quadule/knobby/images/knobby2.jpg

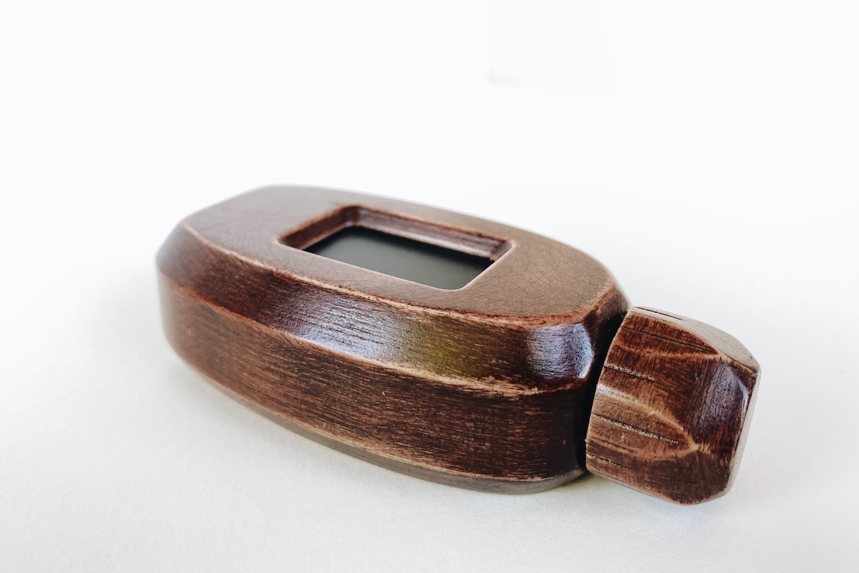
images/knobby2.jpg
