quadule/knobby/images/knobby5.jpg

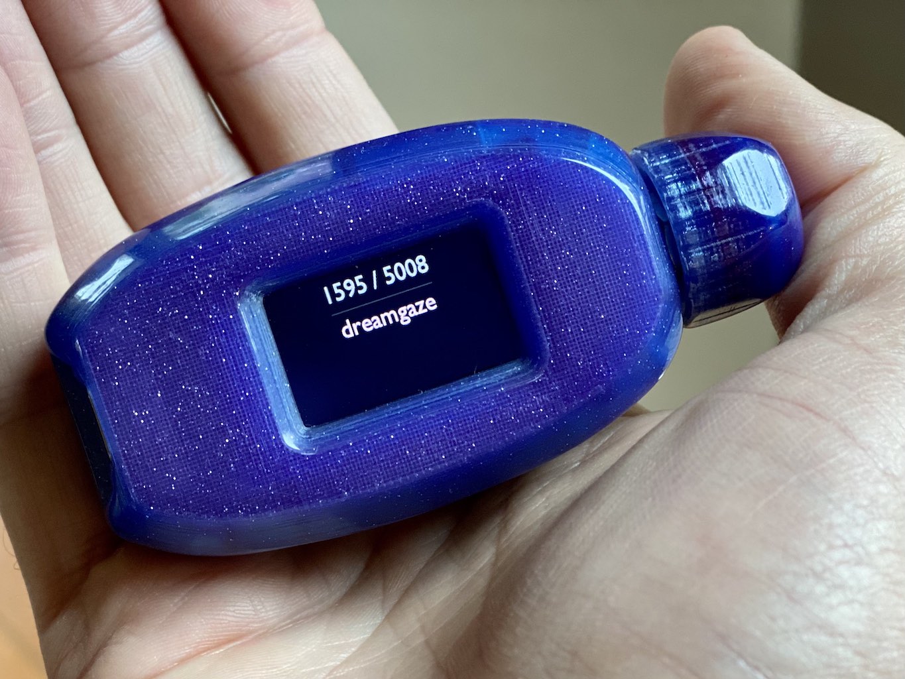
images/knobby5.jpg
