quadule/knobby/src/genres.h

#define GENRE_COUNT 6490
#define COUNTRY_COUNT 201

const char *genres[GENRE_COUNT] = { "2-step", "21st century classical", "432hz", "48g", "528hz", "5th gen k-pop", "5th wave emo", "8-bit", "8d", "a cappella", "a3", "aarhus indie", "aberdeen indie", "abstract", "abstract beats", "abstract hip hop", "abstract idm", "abstractro", "accordeon", "accordion", "accordion band", "acid house", "acid idm", "acid jazz", "acid rock", "acid techno", "acid trance", "acidcore", "acousmatic", "acoustic blues", "acoustic chill", "acoustic cover", "acoustic guitar cover", "acoustic opm", "acoustic pop", "acoustic punk", "acoustic rock", "action rock", "actors", "adelaide indie", "adelaide punk", "adivasi pop", "adoracao", "adoracion", "adoracion pentecostal", "adult standards", "adventista", "aesthetic rap", "afghan pop", "afghan rap", "afghan traditional", "african electronic", "african experimental", "african gospel", "african metal", "african percussion", "african reggae", "african rock", "african shoegaze", "african-american classical", "afrikaans", "afrikaans folk", "afrikaans gospel", "afrikaans gqom", "afrikaans hip hop", "afro drill", "afro house", "afro house angolano", "afro psych", "afro r&b", "afro soul", "afro-cuban percussion", "afro-cuban traditional", "afro-funk", "afrobeat", "afrobeat brasileiro", "afrobeat fusion", "afrobeats", "afrofuturism", "afrofuturismo brasileiro", "afropop", "afroswing", "aggressive phonk", "aggro chileno", "aggrotech", "aghani lil-atfal", "agronejo", "ai", "aikatsu", "ainu folk", "akordeon", "alabama hardcore", "alabama indie", "alabama metal", "alabama rap", "alandsk musik", "alaska hip hop", "alaska indie", "albanian alternative", "albanian folk", "albanian hip hop", "albanian iso polyphony", "albanian pop", "albanian rock", "albany ny indie", "alberta country", "alberta hip hop", "album rock", "albuquerque indie", "algerian folk", "algorave", "alpenpanorama", "alphorn", "alpine yodeling", "alt z", "alt-idol", "alte", "alternative americana", "alternative ccm", "alternative country", "alternative dance", "alternative emo", "alternative hardcore", "alternative hip hop", "alternative metal", "alternative metalcore", "alternative pop", "alternative pop rock", "alternative r&b", "alternative rock", "alternative roots rock", "amapiano", "ambeat", "ambient", "ambient black metal", "ambient country", "ambient dub", "ambient dub techno", "ambient folk", "ambient fusion", "ambient guitar", "ambient house", "ambient idm", "ambient industrial", "ambient lo-fi", "ambient pop", "ambient post-rock", "ambient psychill", "ambient synth", "ambient techno", "ambient trance", "ambient worship", "american 21st century classical", "american choir", "american classical piano", "american contemporary classical", "american early music", "american folk revival", "american grindcore", "american melodeath", "american metalcore", "american modern classical", "american oi", "american orchestra", "american post-punk", "american post-rock", "american primitive", "american romanticism", "american shoegaze", "amharic pop", "anadolu rock", "anarcho-punk", "ancient mediterranean", "andalusian classical", "andean flute", "andean panpipe", "anglican liturgy", "animal singing", "anime", "anime cv", "anime drill", "anime game", "anime hardstyle", "anime latino", "anime lo-fi", "anime phonk", "anime piano", "anime rap", "anime rock", "anime score", "animegrind", "ann arbor indie", "anthem", "anthem emo", "anthem worship", "anti-folk", "antideutsche", "antilliaanse folklore", "antilliaanse rap", "antiviral pop", "apostolic worship", "appalachian black metal", "appalachian folk", "appenzeller folk", "arab alternative", "arab electronic", "arab experimental", "arab folk", "arab groove", "arab metal", "arab pop", "arab trap", "arabesk", "arabic hip hop", "arabic instrumental", "arabic jazz", "argentine alternative rock", "argentine ambient", "argentine hardcore", "argentine heavy metal", "argentine hip hop", "argentine indie", "argentine indie rock", "argentine jazz", "argentine metal", "argentine punk", "argentine reggae", "argentine rock", "argentine telepop", "arizona punk", "arkansas country", "arkansas hip hop", "arkansas indie", "arkansas metal", "armenian folk", "armenian hip hop", "armenian indie", "armenian pop", "arpa grande", "arpa paraguaya", "arrocha", "arrochadeira", "ars subtilior", "art pop", "art punk", "art rock", "art song", "arunachal indie", "asakaa", "asbury park indie", "asheville indie", "asian american hip hop", "asmr", "assamese hip hop", "assamese pop", "assyrian pop", "athens indie", "atl drill", "atl hip hop", "atl trap", "atlanta bass", "atlanta indie", "atlanta metal", "atlanta punk", "atlantic canada hip hop", "atmosphere", "atmospheric black metal", "atmospheric dnb", "atmospheric doom", "atmospheric post-metal", "atmospheric post-rock", "atmospheric sludge", "auckland indie", "audiophile vocal", "aussie drill", "aussie emo", "aussietronica", "austin americana", "austin hip hop", "austin metal", "austin rock", "austin singer-songwriter", "austindie", "australian alt-country", "australian alternative pop", "australian alternative rock", "australian ambient", "australian americana", "australian black metal", "australian blues", "australian children's music", "australian choir", "australian classical", "australian classical piano", "australian comedy", "australian country", "australian dance", "australian death metal", "australian electropop", "australian experimental", "australian garage punk", "australian hardcore", "australian hip hop", "australian house", "australian indie", "australian indie folk", "australian indie rock", "australian indigenous hip hop", "australian indigenous music", "australian jazz", "australian metal", "australian metalcore", "australian pop", "australian post-hardcore", "australian post-punk", "australian post-rock", "australian psych", "australian r&b", "australian reggae fusion", "australian rock", "australian rockabilly", "australian shoegaze", "australian singer-songwriter", "australian ska", "australian surf rock", "australian talent show", "australian techno", "australian thrash metal", "australian trap", "australian underground hip hop", "austrian black metal", "austrian choir", "austrian classical piano", "austrian contemporary classical", "austrian dnb", "austrian hip hop", "austrian indie", "austrian jazz", "austrian metal", "austrian orchestra", "austrian pop", "austrian punk", "austrian stoner rock", "austrian techno", "austro-german modernism", "austropop", "auteur-compositeur-interprete quebecois", "autoharp", "autonomous black metal", "avant-garde", "avant-garde black metal", "avant-garde jazz", "avant-garde metal", "avant-prog", "avant-rock", "axe", "azeri alternative", "azeri pop", "azeri rap", "azeri traditional", "azonto", "azontobeats", "bachata", "bachata dominicana", "bachchon ke geet", "background jazz", "background jazz product", "background music", "background piano", "backing track", "baglama", "bagpipe", "bagpipe marching band", "baha'i", "bahamian folk", "bahamian pop", "baiao", "baithak gana", "baja indie", "bajan soca", "bajki", "bakersfield sound", "bal-musette", "balafon", "balalaika", "balearic", "balfolk", "bali indie", "balikpapan indie", "balinese traditional", "balkan beats", "balkan brass", "balkan classical piano", "balkan drill", "balkan folk metal", "balkan hip hop", "balkan post-punk", "balkan punk", "balkan trap", "ballet class", "ballroom", "balochi folk", "balochi pop", "baltic black metal", "baltic choir", "baltic classical", "baltic classical piano", "baltic folk", "baltic post-punk", "baltimore hip hop", "baltimore indie", "band organ", "banda", "banda carnavalera", "banda de bronces", "banda de viento", "banda guanajuatense", "banda jalisciense", "banda militar", "banda peruana", "banda sinaloense", "bandinhas", "bandolim", "bandoneon", "bandung indie", "bandura", "bangalore indie", "bangla gojol", "bangla pop", "bangladeshi hip hop", "bangladeshi indie", "bangladeshi rock", "banjara pop", "banjo", "bansuri", "baoule", "baps", "baptist gospel", "barbadian pop", "barbershop", "barcadi", "bard", "bardcore", "barnalog", "barnasogur", "barnemusikk", "barnmusik", "barnsagor", "barockinterpreten", "baroque", "baroque brass", "baroque cello", "baroque ensemble", "baroque pop", "baroque singing", "baroque violin", "baroque woodwind", "barrelhouse piano", "basel indie", "bases de freestyle", "basque folk", "bass house", "bass music", "bass trap", "bass trip", "basshall", "bassline", "batak", "bath indie", "batida", "batidao romantico", "baton rouge indie", "baton rouge rap", "batswana traditional", "battle rap", "bay area hip hop", "bay area indie", "bayerischer rap", "bboy", "bc underground hip hop", "beach house", "beach music", "beat italiano", "beat poetry", "beatboxing", "beatdown", "beatlesque", "beats", "bebop", "bedroom pop", "bedroom r&b", "bedroom skramz", "bedroom soul", "belarusian electronic", "belarusian hip hop", "belarusian indie", "belarusian metal", "belarusian pop", "belarusian punk", "belarusian rock", "belfast indie", "belfast metal", "belgian black metal", "belgian blues", "belgian classical piano", "belgian contemporary classical", "belgian dance", "belgian death metal", "belgian dnb", "belgian edm", "belgian electronic", "belgian experimental", "belgian hardcore", "belgian hip hop", "belgian indie", "belgian indie rock", "belgian jazz", "belgian metal", "belgian modern jazz", "belgian new wave", "belgian pop", "belgian post-rock", "belgian punk", "belgian rock", "belgian singer-songwriter", "belgian stoner rock", "belgian techno", "bells", "belly dance", "belo horizonte indie", "bemani", "benga", "bengali folk", "bengali metal", "beninese pop", "bergamo indie", "bergen indie", "berlin minimal techno", "berlin school", "bern indie", "bernu dziesmas", "bgm", "bhajan", "bhangra", "bhojpuri folk", "bhojpuri pop", "bhutanese pop", "bible", "big band", "big beat", "big room", "bikutsi", "binaural", "birdsong", "birmingham grime", "birmingham hip hop", "birmingham indie", "birmingham metal", "birthday", "bisaya indie", "bisaya rap", "bisaya worship", "bisrock", "bitpop", "black 'n' roll", "black americana", "black comedy", "black death", "black metal", "black metal argentino", "black noise", "black punk", "black sludge", "black speed metal", "black thrash", "blackened crust", "blackened deathcore", "blackened hardcore", "blackened screamo", "blackgaze", "blaskapelle", "blasmusik", "bleakgaze", "bleep techno", "bloco", "bluegrass", "bluegrass fiddle", "bluegrass gospel", "blues", "blues band", "blues latinoamericano", "blues mexicano", "blues rock", "blues-rock guitar", "bmore", "bodo pop", "boeremusiek", "bogor indie", "bohemian baroque", "bohol indie", "bolero", "bolero cubano", "bolero mexicano", "bolivian metal", "bolivian rock", "bolobedu house", "bomba", "bomba y plena", "bongo flava", "boogaloo", "boogie", "boogie-woogie", "boom bap", "boom bap brasileiro", "boom bap espanol", "bornehistorier", "borneo traditional", "bornesange", "bosnian electronic", "bosnian indie", "bosnian pop", "bossa nova", "bossa nova cover", "bossa nova jazz", "bossbeat", "bosstown sound", "boston drill", "boston electronic", "boston folk", "boston hardcore", "boston hip hop", "boston indie", "boston metal", "boston punk", "boston rock", "bothy ballad", "botswana hip hop", "botswana pop", "bounce", "bouncy house", "bouyon", "bouzouki", "bow pop", "boy band", "boy pop", "boy soprano", "bozlak", "brain waves", "braindance", "brasilia indie", "brass band", "brass band brasileiro", "brass band pop", "brass ensemble", "brass quintet", "brazilian bass", "brazilian black metal", "brazilian blues", "brazilian boogie", "brazilian ccm", "brazilian classical", "brazilian classical piano", "brazilian contemporary classical", "brazilian death metal", "brazilian dnb", "brazilian doom metal", "brazilian edm", "brazilian emo", "brazilian experimental", "brazilian gospel", "brazilian grindcore", "brazilian groove metal", "brazilian hardcore", "brazilian heavy metal", "brazilian hip hop", "brazilian house", "brazilian indie", "brazilian indie rock", "brazilian jazz", "brazilian lo-fi rock", "brazilian metal", "brazilian metalcore", "brazilian modern jazz", "brazilian percussion", "brazilian post-hardcore", "brazilian post-rock", "brazilian power metal", "brazilian progressive metal", "brazilian punk", "brazilian punk rock", "brazilian reggae", "brazilian rock", "brazilian rockabilly", "brazilian ska", "brazilian soul", "brazilian stoner rock", "brazilian straight edge", "brazilian surf rock", "brazilian tech house", "brazilian techno", "brazilian thrash metal", "breakbeat", "breakcore", "breaks", "brega", "brega funk", "brega paraense", "brega romantico", "brega saudade", "breton folk", "brighton indie", "brill building pop", "brisbane hip hop", "brisbane indie", "brisbane punk", "bristol electronic", "bristol indie", "brit funk", "britcore", "british alternative rock", "british black metal", "british blues", "british brass band", "british children's music", "british choir", "british classical piano", "british comedy", "british contemporary classical", "british country", "british dance band", "british death metal", "british electroacoustic", "british experimental", "british folk", "british grindcore", "british indie rock", "british industrial", "british invasion", "british jazz", "british math rock", "british modern classical", "british orchestra", "british post-rock", "british power metal", "british singer-songwriter", "british soul", "british soundtrack", "britpop", "britpop revival", "brno indie", "broadway", "brockton hip hop", "broken beat", "broken transmission", "bronx drill", "bronx hip hop", "brooklyn drill", "brooklyn indie", "brostep", "bruneian indie", "bruneian pop", "brutal death metal", "brutal deathcore", "brutal prog", "bubble trance", "bubblegrunge", "bubblegum bass", "bubblegum dance", "bubblegum pop", "buffalo hip hop", "buffalo ny indie", "buffalo ny metal", "bulgarian electronic", "bulgarian experimental", "bulgarian folk", "bulgarian hip hop", "bulgarian indie", "bulgarian metal", "bulgarian pop", "bulgarian r&b", "bulgarian rock", "bulgarian trap", "bullerengue", "burkinabe pop", "burkinabe traditional", "burmese pop", "burmese traditional", "burundian pop", "burundian traditional", "bury st edmunds indie", "bush ballad", "byzantine", "c-pop", "c-pop girl group", "c64", "c86", "cabaret", "cajun", "calgary indie", "cali rap", "california hardcore", "calming instrumental", "calypso", "cambodian pop", "cambodian rock", "cambodian traditional", "cambridge choir", "cambridgeshire indie", "cameroonian hip hop", "cameroonian pop", "campursari", "canadian americana", "canadian black metal", "canadian blues", "canadian ccm", "canadian celtic", "canadian children's music", "canadian choir", "canadian classical", "canadian classical piano", "canadian comedy", "canadian contemporary classical", "canadian contemporary country", "canadian contemporary r&b", "canadian country", "canadian death metal", "canadian drill", "canadian electronic", "canadian electropop", "canadian experimental", "canadian folk", "canadian garage rock", "canadian hardcore", "canadian hip hop", "canadian house", "canadian indie", "canadian indie folk", "canadian indie rock", "canadian indigenous hip hop", "canadian indigenous music", "canadian latin", "canadian metal", "canadian metalcore", "canadian modern jazz", "canadian old school hip hop", "canadian pop", "canadian pop punk", "canadian post-hardcore", "canadian post-punk", "canadian post-rock", "canadian psychedelic", "canadian psychedelic rock", "canadian punk", "canadian rock", "canadian rockabilly", "canadian shoegaze", "canadian singer-songwriter", "canadian soundtrack", "canadian stoner rock", "canadian trap", "canadian underground hip hop", "canberra indie", "cancion infantil latinoamericana", "cancion infantil mexicana", "cancion melodica", "cancoes infantis", "candombe", "candomble", "candy pop", "cantaditas", "cantautor", "cantautor catala", "cantautora argentina", "cantautora mexicana", "cante alentejano", "cante flamenco", "canterbury scene", "canti alpini", "canto a tenore", "canto popular uruguayo", "cantonese opera", "cantonese traditional", "cantonese worship", "cantopop", "canzone d'autore", "canzone genovese", "canzone napoletana", "canzone siciliane", "cape breton folk", "cape breton indie", "cape town indie", "cape verdean folk", "capoeira", "caracas indie", "cardiff indie", "caribbean metal", "carimbo", "carnatic", "carnatic instrumental", "carnatic vocal", "carnaval", "carnaval cadiz", "carnaval limburg", "cartoni animati", "cartoon", "cascadia psych", "cascadia shoegaze", "cascadian black metal", "catalan folk", "cathedral choir", "caucasian classical", "caucasian classical piano", "caucasian folk", "cavernous death metal", "ccm", "cdmx indie", "cdo indie", "cedm", "ceilidh", "cello", "cello ensemble", "celtic", "celtic harp", "celtic metal", "celtic punk", "celtic rock", "central american metal", "central asian folk", "central asian hip hop", "cerkes muzikleri", "ceske chvaly", "cha-cha-cha", "chaabi algerien", "chaabi marocain", "chabad niggunim", "chain punk", "chakma pop", "chakra", "chalga", "chamame", "chamame brasilero", "chamber choir", "chamber ensemble", "chamber folk", "chamber orchestra", "chamber pop", "chamber psych", "chamorro pop", "champeta", "channel islands indie", "channel pop", "chanson", "chanson humoristique", "chanson paillarde", "chanson quebecois", "chanson virale", "chant basque", "chant religieux", "chante nwel", "chaotic black metal", "chaotic hardcore", "chapel hill sound", "chapman stick", "charanga", "charango", "charlotte nc indie", "charlottesville indie", "charred death", "charva", "chasidic pop", "chattanooga indie", "chechen pop", "chennai indie", "chhattisgarhi pop", "chicago blues", "chicago bop", "chicago drill", "chicago hardcore", "chicago house", "chicago indie", "chicago mexican", "chicago pop punk", "chicago punk", "chicago rap", "chicago soul", "chicano punk", "chicano rap", "chicha", "chihuahua indie", "children's choir", "children's folk", "children's music", "children's story", "chilean black metal", "chilean hardcore", "chilean indie", "chilean metal", "chilean rock", "chilean techno", "chilena", "chill abstract hip hop", "chill baile", "chill beats", "chill breakcore", "chill dream pop", "chill drill", "chill groove", "chill guitar", "chill house", "chill lounge", "chill out", "chill phonk", "chill pop", "chill r&b", "chill-out trance", "chillhop", "chillstep", "chillsynth", "chillwave", "chimurenga", "chinderlieder", "chinese audiophile", "chinese bgm", "chinese black metal", "chinese classical", "chinese classical performance", "chinese classical piano", "chinese drama ost", "chinese electronic", "chinese electropop", "chinese experimental", "chinese folk", "chinese hip hop", "chinese hyperpop", "chinese idol pop", "chinese indie", "chinese indie pop", "chinese indie rock", "chinese instrumental", "chinese jazz", "chinese manyao", "chinese melodic rap", "chinese metal", "chinese metalcore", "chinese minyao", "chinese new year", "chinese opera", "chinese post-punk", "chinese post-rock", "chinese punk", "chinese r&b", "chinese reggae", "chinese singer-songwriter", "chinese soundtrack", "chinese talent show", "chinese traditional", "chinese viral pop", "chinese wind", "chinese worship", "chip hop", "chiptune", "chopped and screwed", "choral", "choro", "choro contemporaneo", "christchurch indie", "christelijk", "christian a cappella", "christian afrobeat", "christian alternative rock", "christian dance", "christian death metal", "christian deathcore", "christian doom metal", "christian hard rock", "christian hardcore", "christian hip hop", "christian indie", "christian indie folk", "christian lo-fi", "christian metal", "christian metalcore", "christian music", "christian pop", "christian power metal", "christian punk", "christian rock", "christian symphonic metal", "christian thrash metal", "christian trap", "christian uplift", "christlicher rap", "christmas", "christmas instrumental", "christmas product", "chutney", "cifteli", "cimbalom", "cimbalova muzika", "cincinnati indie", "cincinnati rap", "cinematic dubstep", "cinematic post-rock", "circassian folk", "circuit", "circus", "city pop", "clap and tap", "clarinet ensemble", "classic afrobeat", "classic anime", "classic arab pop", "classic assamese pop", "classic australian country", "classic azeri pop", "classic bangla pop", "classic belgian pop", "classic bhangra", "classic bollywood", "classic bulgarian pop", "classic canadian rock", "classic cantopop", "classic city pop", "classic colombian pop", "classic country pop", "classic czech pop", "classic danish pop", "classic danish rock", "classic disco polo", "classic dubstep", "classic dutch pop", "classic eurovision", "classic female blues", "classic finnish pop", "classic finnish rock", "classic french pop", "classic garage rock", "classic girl group", "classic greek pop", "classic greek rock", "classic hardstyle", "classic house", "classic hungarian pop", "classic hungarian rock", "classic icelandic pop", "classic indo pop", "classic indonesian rock", "classic iskelma", "classic israeli pop", "classic italian folk pop", "classic italian pop", "classic j-pop", "classic j-rock", "classic japanese jazz", "classic k-pop", "classic kollywood", "classic konkani pop", "classic korean pop", "classic latvian pop", "classic luk thung", "classic malaysian pop", "classic mandopop", "classic moroccan pop", "classic nepali pop", "classic norwegian pop", "classic nz country", "classic nz pop", "classic oklahoma country", "classic opm", "classic pakistani pop", "classic persian pop", "classic peruvian pop", "classic polish pop", "classic portuguese pop", "classic praise", "classic progressive house", "classic psychedelic rock", "classic punjabi pop", "classic rock", "classic romanian pop", "classic russian pop", "classic russian rock", "classic schlager", "classic sierreno", "classic sinhala pop", "classic soul", "classic soundtrack", "classic sudanese pop", "classic swedish pop", "classic texas country", "classic thai pop", "classic tollywood", "classic tunisian pop", "classic turkish pop", "classic uk pop", "classic ukrainian pop", "classic venezuelan pop", "classical", "classical accordion", "classical baritone", "classical bass", "classical bassoon", "classical cello", "classical clarinet", "classical contralto", "classical countertenor", "classical drill", "classical era", "classical flute", "classical guitar", "classical guitar duo", "classical guitar quartet", "classical harp", "classical horn", "classical jazz fusion", "classical mandolin", "classical mezzo-soprano", "classical oboe", "classical organ", "classical percussion", "classical performance", "classical piano", "classical piano duo", "classical piano quartet", "classical piano trio", "classical saxophone", "classical saxophone quartet", "classical soprano", "classical string trio", "classical tenor", "classical trombone", "classical trumpet", "classical tuba", "classify", "clawhammer banjo", "clean comedy", "cleveland indie", "cleveland metal", "cloud rap", "cloud rap francais", "coco", "cocuk masallari", "cocuk sarkilari", "coldwave", "collage pop", "college a cappella", "college marching band", "cologne electronic", "cologne hip hop", "cologne indie", "colombian black metal", "colombian death metal", "colombian electronic", "colombian hardcore", "colombian hip hop", "colombian indie", "colombian pop", "colombian rock", "color noise", "colorado hardcore", "columbus ohio indie", "combos nacionales", "comedia", "comedie musicale", "comedienne", "comedy", "comedy rap", "comedy rock", "comfy synth", "comic", "comic metal", "commons", "complextro", "compositional ambient", "comptine", "comptine africaine", "concepcion indie", "concert band", "concertina", "concurso de talentos argentino", "congolese gospel", "connecticut hardcore", "connecticut indie", "conscious hip hop", "contemporary choir", "contemporary classical", "contemporary classical piano", "contemporary country", "contemporary folk", "contemporary gospel", "contemporary jazz", "contemporary post-bop", "contemporary r&b", "contemporary vocal jazz", "contra dance", "contrabass", "convent", "cook islands pop", "cool jazz", "copla", "coptic hymn", "coral gospel", "corecore", "cork indie", "cornetas y tambores", "cornish folk", "cornwall indie", "corrido", "corridos adictivos", "corridos alternativos", "corridos belicos", "corridos clasicos", "corridos cristianos", "corridos tumbados", "corrosion", "corsican folk", "cosmic american", "cosmic black metal", "cosmic death metal", "cosmic post-rock", "cosmic uplifting trance", "country", "country blues", "country boogie", "country dawn", "country gospel", "country pop", "country quebecois", "country rap", "country road", "country rock", "countrygaze", "coupe-decale", "coventry indie", "cover acustico", "coverchill", "covertrance", "covertronica", "cowboy western", "cowpunk", "crack rock steady", "crank wave", "cristiana para ninos", "croatian electronic", "croatian folk", "croatian hip hop", "croatian indie", "croatian metal", "croatian pop", "croatian rock", "crossover prog", "crossover thrash", "cruise", "crunk", "crust punk", "cryptic black metal", "cuarteto", "cuatro puertorriqueno", "cuatro venezolano", "cuban alternative", "cuban electronic", "cuban funk", "cuban rumba", "cubaton", "cueca chilena", "cuento infantile", "cumbia", "cumbia 420", "cumbia amazonica", "cumbia andina mexicana", "cumbia boliviana", "cumbia chilena", "cumbia colombiana regia", "cumbia cristiana", "cumbia del sureste", "cumbia ecuatoriana", "cumbia editada", "cumbia funk", "cumbia lagunera", "cumbia paraguaya", "cumbia peruana", "cumbia pop", "cumbia ranchera", "cumbia salvadorena", "cumbia santafesina", "cumbia sonidera", "cumbia sonorense", "cumbia surena", "cumbia uruguaya", "cumbia villera", "cyber metal", "cybergrind", "cyberpunk", "cymraeg", "cypriot hip hop", "cypriot metal", "cypriot pop", "czech alternative rap", "czech classical", "czech classical piano", "czech contemporary classical", "czech country", "czech drill", "czech electronic", "czech experimental", "czech folk", "czech folk rock", "czech hardcore", "czech hip hop", "czech indie", "czech jazz", "czech metal", "czech pop", "czech pop rock", "czech psychedelic", "czech punk", "czech rock", "czech singer-songwriter", "czech swing", "czsk black metal", "czsk electropop", "czsk emo rap", "czsk hip hop", "czsk hyperpop", "czsk reggae", "czsk viral pop", "d-beat", "dabke", "dainuojamoji poezija", "dakke dak", "dalarna indie", "dallas indie", "dambora", "dance pop", "dance rock", "dance-punk", "dancefloor dnb", "dancehall", "dancehall chileno", "dancehall colombiano", "dancehall guyanaise", "dancehall mauricien", "dancehall queen", "dangdut", "dangdut koplo", "dangdut remix", "danish alternative rock", "danish black metal", "danish choir", "danish classical", "danish contemporary classical", "danish death metal", "danish electro", "danish electronic", "danish electropop", "danish experimental", "danish folk", "danish hardcore", "danish hip hop", "danish indie", "danish indie pop", "danish jazz", "danish metal", "danish modern jazz", "danish pop", "danish pop rock", "danish post-punk", "danish punk", "danish rock", "danish singer-songwriter", "danish techno", "dansband", "danseband", "dansei seiyu", "dansk comedy", "dansk lovsang", "dansktop", "danspunk", "danzon", "darbuka", "dariacore", "dark ambient", "dark black metal", "dark cabaret", "dark clubbing", "dark disco", "dark electro", "dark electro-industrial", "dark folk", "dark hardcore", "dark jazz", "dark minimal techno", "dark plugg", "dark pop", "dark post-punk", "dark progressive house", "dark psytrance", "dark r&b", "dark rock", "dark synthpop", "dark techno", "dark trap", "dark wave", "darkstep", "darksynth", "dayton indie", "dc hardcore", "dc indie", "death 'n' roll", "death doom", "death industrial", "death metal", "deathcore", "deathgrass", "deathgrind", "deathrash", "deathrock", "deathstep", "deboxe", "dechovka", "decije pesme", "deconstructed club", "deep acoustic pop", "deep active rock", "deep adult standards", "deep ambient", "deep big room", "deep brazilian pop", "deep breakcore", "deep ccm", "deep chill", "deep chill-out", "deep christian rock", "deep classic garage rock", "deep comedy", "deep contemporary country", "deep dance pop", "deep darkpsy", "deep deep house", "deep deep tech house", "deep delta blues", "deep disco", "deep disco house", "deep discofox", "deep dnb", "deep downtempo fusion", "deep dubstep", "deep east coast hip hop", "deep euro house", "deep eurodance", "deep filthstep", "deep flow", "deep folk metal", "deep free jazz", "deep freestyle", "deep full on", "deep funk", "deep funk house", "deep funk ostentacao", "deep g funk", "deep german hip hop", "deep german indie", "deep german punk", "deep gothic post-punk", "deep groove house", "deep happy hardcore", "deep hardcore", "deep hardcore punk", "deep hardtechno", "deep house", "deep idm", "deep indie pop", "deep indie rock", "deep indie singer-songwriter", "deep italo disco", "deep jazz fusion", "deep latin alternative", "deep latin christian", "deep latin jazz", "deep liquid", "deep liquid bass", "deep melodic death metal", "deep melodic hard rock", "deep melodic metalcore", "deep metalcore", "deep minimal techno", "deep motown", "deep neo-synthpop", "deep neofolk", "deep new americana", "deep new wave", "deep norteno", "deep northern soul", "deep orgcore", "deep pop edm", "deep pop emo", "deep power-pop punk", "deep progressive house", "deep progressive rock", "deep progressive trance", "deep psychobilly", "deep psytrance", "deep punk rock", "deep r&b", "deep ragga", "deep rai", "deep smooth jazz", "deep smooth r&b", "deep soft rock", "deep soul house", "deep soundtrack", "deep southern soul", "deep southern trap", "deep space rock", "deep sunset lounge", "deep surf music", "deep swedish rock", "deep symphonic black metal", "deep talent show", "deep tech house", "deep techno", "deep tropical house", "deep turkish pop", "deep underground hip hop", "deep uplifting trance", "deep vocal house", "deep vocal jazz", "delaware indie", "delta blues", "dembow", "dembow dominicano", "demoscene", "dennery segment", "denpa-kei", "denton tx indie", "denver indie", "denver metal", "denver rap", "depressive black metal", "derby indie", "derry indie", "desert blues", "desi emo rap", "desi hip hop", "desi pop", "desi trap", "dessin anime", "destroy techno", "detroit hardcore", "detroit hip hop", "detroit house", "detroit indie", "detroit rock", "detroit techno", "detroit trap", "detroit trap brasileiro", "detroit trap en espanol", "detske pesnicky", "detske pisnicky", "detski pesnichki", "detskie pesni", "detskie rasskazy", "deutsch disney", "deutschrock", "devon indie", "dfw rap", "dhrupad", "dicsoites", "didgeridoo", "digital hardcore", "dikir barat", "dinner jazz", "dirty south rap", "dirty texas rap", "disco", "disco house", "disco polo", "discofox", "disney", "disney dansk", "disney espanol", "disney horspiele", "disney italiano", "disney norsk", "disney piano", "disney polska", "disney portugues", "disney portugues brasil", "disney russian", "disney suomi", "disney svenska", "dissonant death metal", "diva house", "dixieland", "diy emo", "diy pop punk", "dizi", "djecje pjesme", "djembe", "djent", "dmv rap", "dogri pop", "dombra", "dominican indie", "dominican pop", "dong-yo", "doo-wop", "doom metal", "doomcore", "doomgaze", "dortmund indie", "double drumming", "doujin", "downtempo", "downtempo bass", "downtempo deathcore", "downtempo fusion", "draaiorgel", "draga", "dragspel", "drain", "drama", "dream plugg", "dream pop", "dream trance", "dreamgaze", "dreamo", "dreampunk", "dresden indie", "drift", "drift phonk", "drikkelek", "drill", "drill and bass", "drill beats", "drill brasileiro", "drill chileno", "drill dominicano", "drill espanol", "drill francais", "drill italiana", "drill tuga", "drone", "drone ambient", "drone folk", "drone metal", "drone psych", "drone rock", "dronescape", "drum and bass", "drumfunk", "drumless hip hop", "dub", "dub brasileiro", "dub metal", "dub poetry", "dub product", "dub punk", "dub reggae", "dub techno", "dublin indie", "dubstep", "dubstep product", "dubsteppe", "duduk", "duhovne pjesme", "duluth indie", "dundee indie", "dunedin indie", "dunedin sound", "dungeon rap", "dungeon synth", "duranguense", "dusseldorf electronic", "dusseldorf indie", "dutch americana", "dutch baroque", "dutch black metal", "dutch blues", "dutch cabaret", "dutch classical piano", "dutch contemporary classical", "dutch death metal", "dutch disney", "dutch dnb", "dutch drill", "dutch edm", "dutch experimental", "dutch experimental electronic", "dutch folk", "dutch hip hop", "dutch house", "dutch idol pop", "dutch indie", "dutch indie rock", "dutch jazz", "dutch metal", "dutch moombahton", "dutch musical", "dutch pop", "dutch post-punk", "dutch prog", "dutch punk", "dutch punk rock", "dutch r&b", "dutch rap pop", "dutch rock", "dutch shoegaze", "dutch singer-songwriter", "dutch stoner rock", "dutch tech house", "dutch trance", "dutch trap", "dutch underground hip hop", "dweilorkest", "dytyachi pisni", "early american folk", "early avant garde", "early french punk", "early modern classical", "early music", "early music choir", "early music ensemble", "early reggae", "early romantic era", "early synthpop", "early us punk", "east anglia indie", "east coast hip hop", "east coast reggae", "eastern bloc groove", "easy listening", "easycore", "eau claire indie", "ebm", "ecm-style jazz", "ectofolk", "ecuadorian alternative rock", "ecuadorian indie", "ecuadorian pop", "edinburgh indie", "edinburgh metal", "edm", "edmonton indie", "edo old school", "egg punk", "egyptian alternative", "egyptian hip hop", "egyptian metal", "egyptian pop", "egyptian rock", "egyptian traditional", "egyptian trap", "egyptian viral pop", "el paso indie", "electra", "electric bass", "electric blues", "electro", "electro bailando", "electro dub", "electro house", "electro jazz", "electro latino", "electro swing", "electro trash", "electro-industrial", "electro-pop francais", "electroacoustic composition", "electroacoustic improvisation", "electroclash", "electrofox", "electronic djent", "electronic rock", "electronic trap", "electronica", "electronica argentina", "electronica chilena", "electronica cristiana", "electronica peruana", "electronica venezuela", "electronicore", "electropop", "electropowerpop", "elektropunk", "elephant 6", "eletronica underground brasileira", "emo", "emo mexicano", "emo peruano", "emo punk", "emo rap", "emo rap italiano", "emo trap en espanol", "emo trap italiana", "emocore", "emoplugg", "emotional black metal", "emoviolence", "english baroque", "english indie rock", "english renaissance", "enka", "ensemble stars", "entehno", "environmental", "epa dunk", "epic black metal", "epic collage", "epic doom", "epicore", "epunk", "er ge", "erhu", "eritrean pop", "erotic product", "erotica", "erotik", "escape room", "esperanto", "essex indie", "estonian electronic", "estonian folk", "estonian hip hop", "estonian indie", "estonian jazz", "estonian metal", "estonian pop", "estonian rock", "ethereal gothic", "ethereal wave", "etherpop", "ethio-jazz", "ethiopian hip hop", "ethiopian pop", "ethiopian traditional", "ethnomusicology", "ethnotronica", "eugene indie", "euphonium", "euphoric hardstyle", "euro hi-nrg", "eurobeat", "eurodance", "europop", "euroska", "eurovision", "euskal indie", "euskal metal", "euskal musica", "euskal reggae", "euskal rock", "eventyr", "everything", "exotica", "experimental", "experimental ambient", "experimental bass", "experimental big band", "experimental black metal", "experimental classical", "experimental club", "experimental dub", "experimental dubstep", "experimental electronic", "experimental folk", "experimental guitar", "experimental hip hop", "experimental house", "experimental indie", "experimental indie rock", "experimental jazz", "experimental percussion", "experimental poetry", "experimental pop", "experimental psych", "experimental r&b", "experimental rock", "experimental synth", "experimental techno", "experimental vocal", "extratone", "fado", "fado antigo", "fado de coimbra", "fado instrumental", "fake", "fallen angel", "family gospel", "fan chant", "fantasy", "fantasy metal", "fantasy synth", "faroese folk", "faroese indie", "faroese jazz", "faroese pop", "faroese rock", "fast melodic punk", "festigal", "fictitious orchestra", "fidget house", "field recording", "field recording ambient", "fife and drum", "fijian pop", "filmi", "filter house", "filthstep", "final fantasy", "fingerstyle", "finlandssvenska musik", "finnish alternative rock", "finnish black metal", "finnish blues", "finnish choir", "finnish classical", "finnish contemporary classical", "finnish dance pop", "finnish death metal", "finnish doom metal", "finnish drill", "finnish edm", "finnish electro", "finnish electronic", "finnish experimental", "finnish folk", "finnish hard rock", "finnish hardcore", "finnish heavy metal", "finnish hip hop", "finnish idol pop", "finnish indie", "finnish jazz", "finnish melodeath", "finnish metal", "finnish metalcore", "finnish modern jazz", "finnish new wave", "finnish pop", "finnish pop punk", "finnish post-punk", "finnish power metal", "finnish progressive metal", "finnish progressive rock", "finnish psychedelic rock", "finnish punk", "finnish reggae", "finnish rockabilly", "finnish soul", "finnish tango", "finnish techno", "finnish trap", "finnish worship", "firenze indie", "fisarmonica", "flamenco", "flamenco electronica", "flamenco fusion", "flamenco guitar", "flamenco urbano", "flashcore", "flemish folk", "flick hop", "flint hip hop", "float house", "florida death metal", "florida drill", "florida hardcore", "florida rap", "flute rock", "fluxwork", "fnaf", "fnf", "fo jing", "focus", "focus beats", "focus trance", "fogo pentecostal", "folclor afrocolombiano", "folclor colombiano", "folclore castilla y leon", "folclore extremeno", "folclore jujeno", "folclore navarra", "folclore portugues", "folclore salteno", "folclore santiagueno", "folclore tucumano", "folk", "folk black metal", "folk brasileiro", "folk cantabria", "folk metal", "folk metal latinoamericano", "folk punk", "folk rock", "folk rock italiano", "folk siciliana", "folk-pop", "folklore argentino", "folklore boliviano", "folklore chileno", "folklore cuyano", "folklore ecuatoriano", "folklore nuevo argentino", "folklore panameno", "folklore paraguayo", "folklore peruano", "folklore quebecois", "folklore surero", "folklore uruguayo", "folklore venezolano", "folklore veracruzano", "folkmusik", "folktronica", "football", "footwork", "forest black metal", "forest psy", "forest synth", "forro", "forro de favela", "forro gospel", "forro instrumental", "forro manauara", "forro tradicional", "fort wayne indie", "fort worth indie", "fotbollslatar", "fourth world", "frafra", "franco-flemish school", "frankfurt electronic", "frankfurt indie", "frauenrap", "freak folk", "freakbeat", "free folk", "free improvisation", "free jazz", "freeform hardcore", "freestyle", "fremantle indie", "french baroque", "french black metal", "french classical piano", "french contemporary classical", "french death metal", "french dnb", "french dub", "french emo", "french experimental rock", "french folk", "french folk pop", "french garage rock", "french hardcore", "french hip hop", "french indie folk", "french indie pop", "french indietronica", "french jazz", "french metal", "french movie tunes", "french oi", "french opera", "french orchestra", "french pop", "french post-punk", "french post-rock", "french psychedelic", "french punk", "french reggae", "french renaissance", "french rock", "french rock-and-roll", "french rockabilly", "french romanticism", "french shoegaze", "french soundtrack", "french stoner rock", "french synthpop", "french tech house", "french techno", "french worship", "frenchcore", "frevo", "friese muziek", "fuji", "full on", "full on groove", "funana", "funeral doom", "funk", "funk 150 bpm", "funk bh", "funk capixaba", "funk carioca", "funk consciente", "funk das antigas", "funk evangelico", "funk mandelao", "funk melody", "funk metal", "funk mexicano", "funk mtg", "funk ostentacao", "funk paulista", "funk pop", "funk rj", "funk rock", "funk viral", "funktronica", "funky breaks", "funky house", "funky tech house", "furry", "fussball", "future ambient", "future bass", "future bounce", "future funk", "future garage", "future house", "future rock", "futurepop", "futuristic swag", "fvnky rimex", "g funk", "g-house", "gabber", "gabonese pop", "gaddiyali pop", "gaian doom", "gainesville indie", "gaita", "gaita colombiana", "gaita zuliana", "galante era", "galego", "galician folk", "galician indie", "galician jazz", "galician rock", "galway indie", "gambian hip hop", "gambian pop", "game mood", "gamecore", "gamelan", "gaming dubstep", "gaming edm", "gangster rap", "garage house", "garage pop", "garage psych", "garage punk", "garage punk blues", "garage rock", "garage rock mexicano", "garage rock revival", "garhwali pop", "garifuna folk", "garo pop", "gauze pop", "gay chorus", "gayageum", "gbvfi", "geek folk", "geek rock", "geinin song", "gen z singer-songwriter", "gengetone", "genshin", "georgian alternative", "georgian electronic", "georgian folk", "georgian hip hop", "georgian polyphony", "georgian pop", "georgian rock", "german alternative rap", "german alternative rock", "german baroque", "german black metal", "german blues", "german boom bap", "german ccm", "german choir", "german classical piano", "german cloud rap", "german contemporary classical", "german country", "german dance", "german dark minimal techno", "german death metal", "german dnb", "german drill", "german ebm", "german electronica", "german grindcore", "german hard rock", "german hardcore", "german heavy metal", "german hip hop", "german house", "german hyperpop", "german indie", "german indie folk", "german indie pop", "german indie rock", "german jazz", "german jazz rap", "german literature", "german melodeath", "german metal", "german metalcore", "german oi", "german opera", "german orchestra", "german pagan metal", "german pop", "german pop rock", "german post-hardcore", "german post-punk", "german post-rock", "german power metal", "german prog", "german punk", "german punk rock", "german r&b", "german reggae", "german renaissance", "german rock", "german rockabilly", "german romanticism", "german shoegaze", "german show tunes", "german singer-songwriter", "german ska", "german soundtrack", "german stoner rock", "german street punk", "german tech house", "german techno", "german thrash metal", "german trance", "german trap", "german underground rap", "german viral rap", "german worship", "ghanaian alternative", "ghanaian gospel", "ghanaian hip hop", "ghanaian pop", "ghanaian traditional", "ghazal", "ghent indie", "ghettotech", "ghibli", "ghoststep", "girl group", "glam metal", "glam punk", "glam rock", "glasgow indie", "glass", "glee club", "glitch", "glitch ambient", "glitch beats", "glitch hop", "glitch pop", "glitchbreak", "glitchcore", "glitter trance", "gnawa", "go-go", "goa hip hop", "goa psytrance", "goa trance", "gochiusa", "gogeo", "golden age hip hop", "gong", "goralski", "goregrind", "gorge", "gospel", "gospel amapiano", "gospel antigas", "gospel blues", "gospel drill", "gospel italiano", "gospel papiamento", "gospel r&b", "gospel rap", "gospel reggae", "gospel singers", "gospel soul", "gothabilly", "gothenburg hip hop", "gothenburg indie", "gothenburg metal", "gothic alternative", "gothic americana", "gothic black metal", "gothic doom", "gothic metal", "gothic post-punk", "gothic rock", "gothic symphonic metal", "gotico brasileiro", "gotlandsk musik", "gqom", "granada indie", "grand rapids indie", "grave wave", "graz indie", "grebo", "greek black metal", "greek clarinet", "greek contemporary classical", "greek downtempo", "greek drill", "greek fem rap", "greek folk", "greek guitar", "greek hip hop", "greek house", "greek indie", "greek indie rock", "greek jazz", "greek metal", "greek pop", "greek post-punk", "greek psychedelic rock", "greek punk", "greek rock", "greek shoegaze", "greek swing", "greek techno", "greek trap", "greek underground rap", "greenlandic pop", "gregorian chant", "gregorian dance", "grenada soca", "grim death metal", "grime", "grime brasileiro", "grimewave", "grindcore", "griot", "grisly death metal", "groove gospel", "groove metal", "groove room", "grunge", "grunge argentina", "grunge brasileiro", "grunge pop", "grunge revival", "grungegaze", "grunneger muziek", "grupera", "gruperas inmortales", "grupero romantico", "guadalajara indie", "guam indie", "guaracha", "guaracha santiaguena", "guatemalan indie", "guatemalan metal", "guatemalan pop", "guggenmusik", "guidance", "guided meditation", "guinean pop", "guitar case", "guitarra andina", "guitarra argentina", "guitarra clasica", "guitarra mexicana", "guitarra portuguesa", "gujarati garba", "gujarati pop", "gulf hip hop", "gumbe", "gundam", "guqin", "guyanese pop", "guzheng", "gwoka", "gyerekdalok", "gym hardstyle", "gym phonk", "gymcore", "gypsy", "gypsy fusion", "gypsy jazz", "gypsy punk", "h8000", "haitian dance", "haitian gospel", "haitian traditional", "haitian vodou drumming", "hakkapop", "halftime dnb", "halifax indie", "halloween", "hamburg electronic", "hamburg hip hop", "hamburg indie", "hamburger schule", "hamilton on indie", "hammered dulcimer", "hammond organ", "hampton roads indie", "handbells", "handpan", "hands up", "hangoskonyvek", "happy hardcore", "hard alternative", "hard bass", "hard bop", "hard chime", "hard dance", "hard glam", "hard house", "hard industrial techno", "hard minimal techno", "hard motivation", "hard rock", "hard rock brasileiro", "hard rock mexicano", "hard stoner rock", "hard techno", "hard trance", "hardcore", "hardcore breaks", "hardcore hip hop", "hardcore punk", "hardcore punk espanol", "hardcore techno", "hardgroove", "hardingfele", "hardstyle", "hardtekk", "hardvapour", "hardwave", "hare krishna", "harlem hip hop", "harlem renaissance", "harmonica blues", "harmonica jazz", "harmonikka", "harp", "harpsichord", "harsh noise wall", "haryanvi hip hop", "haryanvi pop", "haryanvi ragni", "hauntology", "haur kantak", "hausa pop", "hawaiian", "hawaiian hip hop", "hawaiian indie", "hawaiian punk", "hazaragi pop", "healing", "healing hz", "heartland rock", "heavy alternative", "heavy gothic rock", "heavy psych", "hel", "heligonka", "hengelliset laulut", "hexd", "hi-nrg", "hi-tech", "high vibe", "high-tech minimal", "highlife", "himachali pop", "himalayan folk", "himene tarava", "hindi hip hop", "hindi indie", "hindi worship", "hindustani classical", "hindustani instrumental", "hindustani vocal", "hinos ccb", "hip hop", "hip hop boliviano", "hip hop cubano", "hip hop galsen", "hip hop mauritanien", "hip hop quebecois", "hip hop reunionnais", "hip hop timur", "hip hop tuga", "hip house", "hip pop", "hip-hop experimental", "hipco", "hiplife", "histoire pour enfants", "historic classical performance", "historic orchestral performance", "historic piano performance", "historic string quartet", "historical keyboard", "historically informed performance", "hjemmesnekk", "hk-pop", "hmong pop", "ho munda", "hoerspiel", "hokkaido indie", "hokkien pop", "hollywood", "hololive", "honeyworks", "hong kong hip hop", "hong kong indie", "hong kong rock", "hong kong tv drama", "honky tonk", "honky-tonk piano", "hopebeat", "horn ensemble", "horo", "horror punk", "horror punk brasileiro", "horror synth", "horrorcore", "hot jazz", "house", "house argentino", "houston indie", "houston rap", "huapango", "huayno", "huayno peruano", "huayno popular", "hula", "hull indie", "humour francais", "humppa", "hungarian black metal", "hungarian choir", "hungarian classical performance", "hungarian classical piano", "hungarian contemporary classical", "hungarian edm", "hungarian folk", "hungarian hip hop", "hungarian indie", "hungarian metal", "hungarian pop", "hungarian punk", "hungarian rock", "hungarian techno", "hungarian underground rap", "huqin", "hurdy-gurdy", "huzunlu sarkilar", "hyper-rock", "hyperpop", "hyperpop brasileiro", "hyperpop en espanol", "hyperpop francais", "hyperpop italiano", "hypertechno", "hypertrance", "hyphy", "hypnagogic pop", "hypnosis", "hypnosis mic", "hypnotic techno", "icelandic black metal", "icelandic choir", "icelandic classical", "icelandic electronic", "icelandic experimental", "icelandic folk", "icelandic hip hop", "icelandic indie", "icelandic jazz", "icelandic metal", "icelandic pop", "icelandic post-punk", "icelandic punk", "icelandic rock", "icelandic singer-songwriter", "icelandic traditional", "idaho hip hop", "idaho indie", "idol", "idol game", "idol kayo", "idol rock", "igbo pop", "igbo rap", "igbo traditional", "igbo trap", "igbo worship", "ilahije", "ilahiler", "illbient", "ilocano pop", "impressionism", "indian ambient", "indian classical", "indian edm", "indian electronic", "indian folk", "indian fusion", "indian indie", "indian instrumental", "indian instrumental rock", "indian jazz", "indian lo-fi", "indian metal", "indian percussion", "indian rock", "indian singer-songwriter", "indian techno", "indian underground rap", "indian violin", "indiana hip hop", "indiana indie", "indie anthem-folk", "indie arequipeno", "indie asturiana", "indie boliviano", "indie campechano", "indie canario", "indie cantabria", "indie caribe colombiano", "indie catala", "indie catracho", "indie cordoba", "indie cristao", "indie curitibano", "indie dream pop", "indie electronica", "indie electropop", "indie emo", "indie emo rock", "indie extremena", "indie folk", "indie folk argentino", "indie folk italiano", "indie fuzzpop", "indie game soundtrack", "indie garage rock", "indie hidalguense", "indie hidrocalido", "indie hip hop", "indie huancaino", "indie jazz", "indie liguria", "indie michoacano", "indie napoletano", "indie nica", "indie nordeste argentino", "indie paraense", "indie platense", "indie poblano", "indie pop", "indie pop rap", "indie pop rock", "indie poptimism", "indie psych-pop", "indie psychedelic rock", "indie punk", "indie quebecois", "indie queretano", "indie r&b", "indie rock", "indie rock colombiano", "indie rock italiano", "indie rock mexicano", "indie rock peruano", "indie rockism", "indie salvadoreno", "indie shoegaze", "indie siciliano", "indie singer-songwriter", "indie soul", "indie sudcaliforniano", "indie surf", "indie tabasqueno", "indie tico", "indie triste", "indie trujillano", "indie tucumano", "indie valenciana", "indie veneto", "indie viet", "indiecoustica", "indietronica", "indonesian alternative rock", "indonesian bamboo", "indonesian black metal", "indonesian blues", "indonesian city pop", "indonesian death metal", "indonesian deathcore", "indonesian edm", "indonesian electronic", "indonesian emo", "indonesian emo rap", "indonesian experimental", "indonesian folk", "indonesian folk pop", "indonesian gothic metal", "indonesian hardcore", "indonesian hip hop", "indonesian hyperpop", "indonesian idol pop", "indonesian indie", "indonesian indie pop", "indonesian indie rock", "indonesian indigenous traditional", "indonesian jazz", "indonesian lo-fi pop", "indonesian metal", "indonesian neo-psychedelia", "indonesian pop", "indonesian pop punk", "indonesian pop rock", "indonesian post-hardcore", "indonesian post-punk", "indonesian psychedelia", "indonesian punk", "indonesian r&b", "indonesian reggae", "indonesian rock", "indonesian shoegaze", "indonesian singer-songwriter", "indonesian ska", "indonesian stoner rock", "indonesian thrash metal", "indonesian trap", "indonesian underground hip hop", "indonesian viral pop", "indonesian worship", "indorock", "industrial", "industrial black metal", "industrial hardcore", "industrial hip hop", "industrial metal", "industrial noise", "industrial pop", "industrial rock", "industrial techno", "indy indie", "inland empire hardcore", "instrumental acoustic guitar", "instrumental black metal", "instrumental bluegrass", "instrumental death metal", "instrumental djent", "instrumental funk", "instrumental grime", "instrumental hip hop", "instrumental lullaby", "instrumental math rock", "instrumental post-rock", "instrumental progressive metal", "instrumental rock", "instrumental soul", "instrumental stoner rock", "instrumental surf", "instrumental worship", "intelligent dance music", "inuit pop", "inuit traditional", "iowa hip hop", "iowa indie", "iranian experimental", "iranian metal", "iraqi hip hop", "irish accordion", "irish ballad", "irish banjo", "irish black metal", "irish classical", "irish contemporary classical", "irish country", "irish dance", "irish death metal", "irish drill", "irish electronic", "irish experimental", "irish experimental electronic", "irish fiddle", "irish flute", "irish folk", "irish gaelic folk", "irish hardcore", "irish hip hop", "irish indie", "irish indie rock", "irish metal", "irish modern jazz", "irish neo-traditional", "irish pop", "irish post-punk", "irish pub song", "irish punk", "irish rebel song", "irish rock", "irish shoegaze", "irish singer-songwriter", "irish techno", "irish trap", "irish underground rap", "iskelma", "islamic recitation", "isle of man indie", "isle of wight indie", "israeli classical", "israeli classical piano", "israeli folk", "israeli hip hop", "israeli indie", "israeli jazz", "israeli mediterranean", "israeli metal", "israeli pop", "israeli punk", "israeli rock", "israeli singer-songwriter", "israeli techno", "israeli traditional", "israeli trap", "israelite hip hop", "italian adult pop", "italian alternative", "italian baritone", "italian baroque", "italian baroque ensemble", "italian bass", "italian black metal", "italian blues", "italian choir", "italian classical guitar", "italian classical piano", "italian contemporary classical", "italian contemporary jazz", "italian death metal", "italian doom metal", "italian electronica", "italian emo", "italian experimental", "italian folk", "italian folk metal", "italian gothic", "italian gothic metal", "italian hardcore", "italian heavy metal", "italian hip hop", "italian indie pop", "italian industrial", "italian jazz", "italian jazz fusion", "italian library music", "italian lounge", "italian mandolin", "italian metal", "italian metalcore", "italian mezzo-soprano", "italian modern prog", "italian new wave", "italian occult psychedelia", "italian opera", "italian orchestra", "italian pop", "italian pop punk", "italian pop rock", "italian post-hardcore", "italian post-punk", "italian post-rock", "italian power metal", "italian progressive metal", "italian progressive rock", "italian punk", "italian reggae", "italian renaissance", "italian rockabilly", "italian romanticism", "italian screamo", "italian ska", "italian soprano", "italian soundtrack", "italian stoner rock", "italian tech house", "italian techno", "italian tenor", "italian trance", "italian underground hip hop", "italian violin", "italo beats", "italo dance", "italo disco", "italo house", "italogaze", "izvorna muzika", "j-acoustic", "j-ambient", "j-core", "j-division", "j-idol", "j-indie", "j-metal", "j-pixie", "j-pop", "j-pop boy group", "j-pop girl group", "j-poprock", "j-punk", "j-rap", "j-reggae", "j-rock", "jackin' house", "jacksonville indie", "jain bhajan", "jalsat", "jam band", "jamaican dancehall", "jamaican hip hop", "jamaican ska", "jamgrass", "jamtronica", "jangle pop", "jangle rock", "japanese alternative pop", "japanese alternative rock", "japanese beats", "japanese bedroom pop", "japanese black metal", "japanese blues", "japanese boom bap", "japanese buddhist chant", "japanese celtic", "japanese chill rap", "japanese chillhop", "japanese choir", "japanese classical", "japanese classical performance", "japanese classical piano", "japanese concert band", "japanese contemporary classical", "japanese dance pop", "japanese death metal", "japanese disney", "japanese dream pop", "japanese drill", "japanese dub", "japanese edm", "japanese electronic", "japanese electropop", "japanese emo", "japanese experimental", "japanese flute", "japanese folk", "japanese garage rock", "japanese girl punk", "japanese guitar", "japanese hardcore", "japanese heavy metal", "japanese house", "japanese hyperpop", "japanese idm", "japanese indie folk", "japanese indie pop", "japanese indie rock", "japanese instrumental", "japanese jazz", "japanese jazz fusion", "japanese jazztronica", "japanese juke", "japanese math rock", "japanese melodic hardcore", "japanese melodic punk", "japanese metalcore", "japanese new wave", "japanese old school hip hop", "japanese orchestra", "japanese piano", "japanese pop punk", "japanese pop rap", "japanese post-hardcore", "japanese post-punk", "japanese post-rock", "japanese power metal", "japanese prog", "japanese progressive house", "japanese psychedelic", "japanese psychedelic rock", "japanese punk rock", "japanese r&b", "japanese rockabilly", "japanese screamo", "japanese shoegaze", "japanese singer-songwriter", "japanese ska", "japanese soul", "japanese soundtrack", "japanese techno", "japanese teen pop", "japanese traditional", "japanese trap", "japanese underground rap", "japanese vgm", "japanese viral pop", "japanese vocal jazz", "japanese vtuber", "japanese worship", "japanoise", "javanese dangdut", "javanese gamelan", "jaw harp", "jawaiian", "jazz", "jazz accordion", "jazz blues", "jazz boliviano", "jazz boom bap", "jazz brass", "jazz caraibes", "jazz catala", "jazz chileno", "jazz clarinet", "jazz colombiano", "jazz composition", "jazz cover", "jazz cubano", "jazz dominicano", "jazz double bass", "jazz drums", "jazz flute", "jazz funk", "jazz fusion", "jazz guitar", "jazz guitar trio", "jazz harp", "jazz house", "jazz metal", "jazz mexicano", "jazz orchestra", "jazz organ", "jazz piano", "jazz pop", "jazz puertorriqueno", "jazz quartet", "jazz rap", "jazz rock", "jazz saxophone", "jazz tico", "jazz trio", "jazz trombone", "jazz trumpet", "jazz tuba", "jazz venezolano", "jazz vibraphone", "jazz violin", "jazz worship", "jazzcore", "jazztronica", "jazzy dnb", "jersey club", "jesus movement", "jewish a capella", "jewish cantorial", "jewish hip hop", "jewish pop", "jig and reel", "jirai kei", "jordanian alternative", "jordanian pop", "joropo", "josei rap", "joseon pop", "jota aragonesa", "jovem guarda", "judaica", "jug band", "jugendchor", "juju", "jump blues", "jump up", "jumpstyle", "jumptek", "jungle", "junior eurovision", "junior songfestival", "k-indie", "k-pop", "k-pop ballad", "k-pop boy group", "k-pop girl group", "k-pop reality show", "k-rap", "k-rock", "kaba gaida", "kabarett", "kabyle", "kabyle moderne", "kadongo kamu", "kalmar indie", "kamba pop", "kamen rider", "kaneka", "kannada bhava geethe", "kannada hip hop", "kannada indie", "kannada pop", "kansai indie", "kansas city hip hop", "kansas hip hop", "kansas indie", "kantele", "kapa haka", "karadeniz pop", "karadeniz turkuleri", "karaoke", "karbi pop", "karelian folk", "karen pop", "karneval", "karntner volksmusik", "kaseko", "kashmiri hip hop", "kashmiri pop", "kasi rap", "kavkaz", "kawaii edm", "kawaii future bass", "kawaii metal", "kayokyoku", "kazakh hip hop", "kazakh indie", "kazakh pop", "kazakh traditional", "kazakh viral pop", "kc indie", "keller synth", "kelowna bc indie", "kent indie", "kentucky hip hop", "kentucky indie", "kentucky metal", "kentucky mountain folk", "kentucky punk", "kentucky roots", "kenyan alternative", "kenyan drill", "kenyan hip hop", "kenyan pop", "kenyan r&b", "kenyan traditional", "kerkkoor", "kermis", "keroncong", "khaleeji iraqi", "khaliji", "khandeshi pop", "khasi pop", "khayal", "khmer", "khmer hip hop", "khortha pop", "kids dance party", "kids hip hop", "kikuyu gospel", "kikuyu pop", "kinderchor", "kinderliedjies", "kindermusik", "kindie rock", "king of prism", "kingston on indie", "kinnauri pop", "kirtan", "kiwi rock", "kizomba", "kizomba antigas", "kizomba cabo-verdiana", "klapa", "kleine hoerspiel", "kleinkunst", "klezmer", "klubowe", "knoxville indie", "kodomo no ongaku", "kokborok pop", "kol isha", "koledy", "koligeet", "kolkata indie", "kollywood", "kolo", "kolsche karneval", "komedi", "kompa", "kompa chretien", "kompa gouyad", "konkani pop", "konsrock", "kora", "korean bl ost", "korean city pop", "korean classical performance", "korean classical piano", "korean contemporary classical", "korean dream pop", "korean drill", "korean electronic", "korean electropop", "korean experimental", "korean hardcore", "korean hyperpop", "korean indie folk", "korean indie rock", "korean instrumental", "korean jazz", "korean metal", "korean minyo", "korean musicals", "korean old school hip hop", "korean ost", "korean phantom singer", "korean pop", "korean punk", "korean r&b", "korean shoegaze", "korean singer-songwriter", "korean soundtrack", "korean superband", "korean talent show", "korean traditional", "korean trap", "korean underground rap", "korean worship", "kosovan folk", "kosovan indie", "kosovan pop", "koto", "krajiska muzika", "krautrock", "krishnacore", "kritika", "krushclub", "krushfunk", "kuduro", "kuduro antigo", "kumaoni pop", "kundalini", "kundiman", "kurdish folk", "kurdish hip hop", "kurdish pop", "kurdish remix", "kurdish rock", "kwaito", "kyrgyz hip hop", "kyrgyz pop", "kyrgyz traditional", "kyushu indie", "la hardcore", "la indie", "la pop", "laboratorio", "ladakhi pop", "lafayette indie", "lagu aceh", "lagu bali", "lagu betawi", "lagu bugis", "lagu iban", "lagu jambi", "lagu jawa", "lagu karo", "lagu lampung", "lagu madura", "lagu maluku", "lagu manado", "lagu melayu", "lagu sabahan", "lagu sasak", "lagu sunda", "lagu tarling", "lagu timur", "lai hla", "laiko", "lambadao", "lampung indie", "lancashire indie", "lancaster pa indie", "landler", "language", "lao hip hop", "lao pop", "lao traditional", "lapland hip hop", "lapland metal", "lastelaulud", "lasten satuja", "lata", "late romantic era", "latin", "latin afrobeat", "latin alternative", "latin american baroque", "latin american classical piano", "latin american heavy psych", "latin arena pop", "latin christian", "latin classical", "latin funk", "latin hip hop", "latin house", "latin jazz", "latin metal", "latin pop", "latin rock", "latin shoegaze", "latin ska", "latin soundtrack", "latin surf rock", "latin talent show", "latin tech house", "latin tek", "latin viral pop", "latin viral rap", "latin worship", "latincore", "latino comedy", "latintronica", "latinx alternative", "latmiya", "latvian electronic", "latvian folk", "latvian hip hop", "latvian indie", "latvian metal", "latvian pop", "latvian rock", "laulaja-lauluntekija", "lawrence ks indie", "lds", "lds instrumental", "lds youth", "lebanese indie", "lebanese pop", "leeds indie", "leicester indie", "leipzig electronic", "leipzig indie", "leon gto indie", "lesen", "lesotho traditional", "levenslied", "lexington ky indie", "lezginka", "lgbtq+ hip hop", "liberian pop", "library music", "libyan hip hop", "libyan pop", "liechtenstein", "liedermacher", "light music", "lilith", "limerick indie", "liminal space", "lincoln ne indie", "lion city hardcore", "liquid funk", "lithuanian edm", "lithuanian electronic", "lithuanian folk", "lithuanian hip hop", "lithuanian indie", "lithuanian jazz", "lithuanian metal", "lithuanian pop", "lithuanian rock", "lithuanian trap", "little rock indie", "liverpool indie", "livetronica", "lldm", "lo star", "lo-fi", "lo-fi beats", "lo-fi brasileiro", "lo-fi chill", "lo-fi cover", "lo-fi emo", "lo-fi house", "lo-fi indie", "lo-fi jazzhop", "lo-fi latino", "lo-fi product", "lo-fi rap", "lo-fi sleep", "lo-fi study", "lo-fi vgm", "lok dohori", "lombok indie", "london indie", "london on indie", "london rap", "long island punk", "louange", "louisiana blues", "louisiana metal", "louisville indie", "louisville underground", "lounge", "lounge house", "louvor", "louvor icm", "louvores pentecostais", "love live", "lovecraftian metal", "lovers rock", "lowercase", "lowlands hardcore", "luk thung", "lullaby", "lund indie", "lustrum", "lute", "luxembourgian electronic", "luxembourgian hip hop", "luxembourgian indie", "luxembourgian metal", "luxembourgian pop", "macau pop", "macedonian electronic", "macedonian folk", "macedonian hip hop", "macedonian indie", "macedonian metal", "macedonian pop", "macedonian rock", "macross", "madchester", "madrigal", "maga rap", "maghreb", "maghreb metal", "magyar alternative", "magyar kabare", "magyar mulatos", "magyar musicalek", "magyar retro dance", "magyar trap", "mahraganat", "maidcore", "maimouna", "maine hip hop", "maine indie", "mainland chinese pop", "mainland se asia metal", "maithili", "makina", "makossa", "malagasy folk", "malagasy pop", "malang indie", "malang punk", "malawian folk", "malawian gospel", "malawian hip hop", "malawian pop", "malay rap", "malayalam cover", "malayalam hip hop", "malayalam indie", "malayalam madh", "malayalam pop", "malayalam worship", "malaysian hardcore", "malaysian hip hop", "malaysian indie", "malaysian mandopop", "malaysian metal", "malaysian pop", "malaysian post-rock", "malaysian punk", "malaysian tamil pop", "malaysian tamil rap", "malaysian traditional", "maldivian pop", "malian blues", "malian traditional", "mallet", "mallsoft", "malmo indie", "maloya", "maltese hip hop", "maltese metal", "maltese pop", "maluku pop", "mambo", "mambo chileno", "man's orchestra", "manchester hip hop", "manchester indie", "mande pop", "mandible", "mandolin", "mandopop", "manele", "manguebeat", "manila sound", "manipuri pop", "manitoba country", "manitoba indie", "manso indie", "mantra", "mapouka", "mappila paattu", "maracatu", "marathi balgeet", "marathi devotional", "marathi hip hop", "marathi pop", "marathi remix", "marathi traditional", "marcha funebre", "marching band", "marci brijuzi", "mariachi", "mariachi cristiano", "marimba", "marimba de guatemala", "marimba mexicana", "marimba orquesta", "marinera", "marrabenta", "marsmuziek", "martial industrial", "marwadi pop", "mashcore", "mashup", "maskandi", "massage", "math pop", "math rock", "math rock latinoamericano", "mathcore", "mathgrind", "mazandarani folk", "mbalax", "mbira", "mecha", "medieval", "medieval black metal", "medieval ensemble", "medieval folk", "medieval rock", "medimeisterschaften", "meditation", "medway sound", "meenawati", "mega funk", "melancholia", "melanesian pop", "melbourne bounce", "melbourne bounce international", "melbourne hip hop", "melbourne indie", "melbourne punk", "mellow gold", "melodic black metal", "melodic death metal", "melodic deathcore", "melodic doom", "melodic drill", "melodic dubstep", "melodic groove metal", "melodic hard rock", "melodic hardcore", "melodic house", "melodic metal", "melodic metalcore", "melodic power metal", "melodic progressive metal", "melodic rap", "melodic techno", "melodic thrash", "melodipop", "meme", "meme rap", "memphis americana", "memphis blues", "memphis hip hop", "memphis indie", "memphis phonk", "memphis soul", "men chika", "men's choir", "mento", "merengue", "merengue tipico", "merida indie", "merseybeat", "messianic praise", "mestissatge", "metal", "metal baiano", "metal balear", "metal catala", "metal catarinense", "metal cearense", "metal colombiano", "metal cover", "metal cristao", "metal ecuatoriano", "metal galego", "metal gaucho", "metal gotico", "metal guitar", "metal mineiro", "metal noir quebecois", "metal nortista", "metal paraguayo", "metal paranaense", "metal pernambucano", "metal piauiense", "metal salvadoreno", "metal tico", "metal uruguayo", "metalcore", "metalcore espanol", "metallic hardcore", "metis fiddle", "metropopolis", "mevlevi sufi", "mewati pop", "mexican black metal", "mexican classic rock", "mexican classical", "mexican death metal", "mexican edm", "mexican electronic", "mexican experimental", "mexican hardcore", "mexican hip hop", "mexican indie", "mexican metal", "mexican pop", "mexican pop punk", "mexican post-rock", "mexican power metal", "mexican rock", "mexican rock-and-roll", "mexican son", "mexican tech house", "mexican techno", "mexican thrash metal", "mexican traditional", "meyxana", "mezmur", "mezwed", "mgpjr", "miami bass", "miami electronic", "miami hip hop", "miami indie", "miami metal", "michigan folk", "michigan indie", "microhouse", "microsound", "microtonal", "middle earth", "middle east hip hop", "middle eastern black metal", "middle eastern traditional", "midwest americana", "midwest emo", "midwest shoegaze", "milan indie", "military band", "military cadence", "military rap", "milwaukee hip hop", "milwaukee indie", "min'yo", "mincecore", "mindfulness", "minecraft", "minimal dnb", "minimal dub", "minimal dubstep", "minimal melodic techno", "minimal synth", "minimal tech house", "minimal techno", "minimal wave", "minimalism", "minneapolis indie", "minneapolis metal", "minneapolis punk", "minneapolis sound", "minnesang", "minnesota hip hop", "minnesota metal", "mising pop", "mississippi hip hop", "mississippi indie", "missouri indie", "mizo gospel", "mizo pop", "mizrahi", "mluvene slovo", "mod revival", "modern alternative pop", "modern alternative rock", "modern bhajan", "modern big band", "modern blues", "modern blues rock", "modern bollywood", "modern cello", "modern chamber music", "modern country pop", "modern country rock", "modern darkwave", "modern downshift", "modern dream pop", "modern ebm", "modern electroacoustic", "modern enka", "modern folk rock", "modern free jazz", "modern funk", "modern goth", "modern hard rock", "modern hardcore", "modern indie folk", "modern indie pop", "modern j-rock", "modern jangle pop", "modern jazz piano", "modern jazz trio", "modern jungle", "modern melodic hardcore", "modern mod", "modern old-time", "modern performance", "modern power pop", "modern progressive rock", "modern psychedelic folk", "modern reggae", "modern rock", "modern salsa", "modern ska punk", "modern southern rock", "modern string quartet", "modern swing", "modern uplift", "moderne ludovky", "modular synth", "modular techno", "molam", "moldovan pop", "mollywood", "mongolian alternative", "mongolian folk", "mongolian hip hop", "mongolian pop", "montana indie", "montana metal", "montana roots", "montenegrin pop", "monterrey indie", "montreal indie", "moog", "moombahton", "moorish traditional", "moravian folk", "morelos indie", "morna", "moroccan pop", "moroccan rock", "moroccan traditional", "motivation", "motown", "mountain dulcimer", "movie tunes", "mpb", "mpb gospel", "multidisciplinary", "mumbai indie", "mundart", "munich electronic", "munich indie", "murcia indie", "murga", "music box", "music hall", "musica acoriana", "musica acreana", "musica afroperuana", "musica aguascalentense", "musica alagoana", "musica amapaense", "musica andina", "musica andina chilena", "musica andina colombiana", "musica andorra", "musica angolana", "musica antigua", "musica aragonesa", "musica ayacuchana", "musica baiana", "musica bajacaliforniana", "musica bautista", "musica blumenauense", "musica brasiliense", "musica cabo-verdiana", "musica calabrese", "musica campechana", "musica campineira", "musica campista", "musica canaria", "musica capixaba", "musica caririense", "musica catalana", "musica catarinense", "musica cearense", "musica chiapaneca", "musica chihuahuense", "musica coahuilense", "musica colimense", "musica colombiana instrumental", "musica costarricense", "musica costena", "musica criolla", "musica crista reformada", "musica cristiana guatemalteca", "musica de fondo", "musica de intervencao", "musica duranguense", "musica ecuatoguineana", "musica eletronica brasileira", "musica eletronica gospel", "musica etnica", "musica evangelica instrumental", "musica feirense", "musica folk asturiana", "musica gaucha", "musica gaucha tradicionalista", "musica goiana", "musica guerrerense", "musica guineense", "musica hondurena", "musica indigena brasileira", "musica indigena latinoamericana", "musica indigena mexicana", "musica infantil", "musica infantil catala", "musica instrumental cristiana", "musica istmena", "musica jalisciense", "musica jibara", "musica juiz-forana", "musica llanera", "musica lombarda", "musica londrinense", "musica madeirense", "musica mallorquina", "musica mapuche", "musica maranhense", "musica maringaense", "musica mato-grossense", "musica menorquina", "musica mexicana", "musica mexiquense", "musica michoacana", "musica mixteca", "musica mocambicana", "musica mogiana", "musica morelense", "musica nayarita", "musica neoleonesa", "musica nicaraguense", "musica nortena chilena", "musica nublensina", "musica oaxaquena", "musica occitana", "musica otavalena", "musica para criancas", "musica para ninos", "musica paraibana", "musica paranaense", "musica per bambini", "musica pernambucana", "musica piauiense", "musica piemonteisa", "musica pitiusa", "musica poblana", "musica ponta-grossense", "musica popular amazonense", "musica popular colombiana", "musica popular mineira", "musica popular paraense", "musica popular uruguaya", "musica portuguesa contemporanea", "musica potiguar", "musica potosina", "musica prehispanica", "musica puntana", "musica purepecha", "musica queretana", "musica quintanarroense", "musica rapa nui", "musica rondoniense", "musica roraimense", "musica sammarinese", "musica santomense", "musica sarda", "musica sergipana", "musica sinaloense", "musica sinfonica", "musica sonorense", "musica sudcaliforniana", "musica sul-mato-grossense", "musica tabasquena", "musica tamaulipeca", "musica timor-leste", "musica tlaxcalteca", "musica tocantinense", "musica tradicional cubana", "musica tradicional dominicana", "musica triste brasileira", "musica tropical guatemalteca", "musica urbana oaxaquena", "musica valenciana", "musica wixarika", "musica yucateca", "musical advocacy", "musicas espiritas", "musiikkia lapista", "musiikkia lapsille", "musik anak-anak", "musikkorps", "musiqi-ye zanan", "musique acadienne", "musique alsacienne", "musique ancienne", "musique centrafricaine", "musique comorienne", "musique concrete", "musique guadeloupe", "musique mahoraise", "musique mandingue", "musique mariage algerien", "musique mauritanienne", "musique militaire", "musique nigerienne", "musique peule", "musique pour enfant quebecois", "musique pour enfants", "musique soninke", "musique tahitienne", "musique tchadienne", "musique touareg", "musique traditionnelle comorienne", "musique traditionnelle congolaise", "musique urbaine brazzaville", "musique urbaine kinshasa", "muzica ardeleneasca", "muzica banateana", "muzica bisericeasca", "muzica copii", "muzica crestina", "muzica etno", "muzica lautareasca", "muzica maramureseana", "muzica moldoveneasca", "muzica populara", "muzica usoara", "muziek voor kinderen", "muzika l'yeladim", "myanmar gospel", "myanmar hip hop", "myanmar indie", "naat", "nadaswaram", "nagaland indie", "nagpuri pop", "naija old school", "naija worship", "namibian pop", "nantes indie", "narco rap", "narodna muzika", "narodnozabavna", "nasheed", "nashville americana", "nashville hip hop", "nashville indie", "nashville singer-songwriter", "nashville sound", "nasyid", "native american black metal", "native american contemporary", "native american flute", "native american hip hop", "native american metal", "native american spiritual", "native american traditional", "naturjodel", "navajo", "ndombolo", "neapolitan funk", "necrogrind", "necrotrap", "nederlandse hardstyle", "nederpop", "nederreggae", "neo classical metal", "neo grime", "neo honky tonk", "neo kyma", "neo mellow", "neo metal", "neo r&b", "neo soul", "neo soul-jazz", "neo-classical", "neo-crust", "neo-industrial rock", "neo-kraut", "neo-manele", "neo-pagan", "neo-progressive", "neo-proto", "neo-psicodelia brasileira", "neo-psychedelic", "neo-rockabilly", "neo-shibuya-kei", "neo-singer-songwriter", "neo-synthpop", "neo-trad doom metal", "neo-trad metal", "neo-trad prog", "neo-traditional bluegrass", "neo-traditional country", "neoclassical darkwave", "neoclassicism", "neofolk", "neomelodici", "neon pop punk", "neoperreo", "neotango", "nepali indie", "nepali metal", "nepali pop", "nepali rock", "nephop", "nerdcore", "nerdcore brasileiro", "neru", "neue deutsche harte", "neue deutsche todeskunst", "neue deutsche welle", "neue neue deutsche welle", "neue volksmusik", "neurofunk", "neurostep", "new age", "new age piano", "new americana", "new beat", "new brunswick indie", "new comedy", "new delhi indie", "new england americana", "new england black metal", "new england emo", "new england experimental", "new england hardcore", "new england metal", "new england shoegaze", "new french touch", "new hampshire indie", "new isolationism", "new italo disco", "new jack smooth", "new jack swing", "new jersey hardcore", "new jersey indie", "new jersey punk", "new jersey rap", "new jersey underground rap", "new mexico music", "new orleans americana", "new orleans blues", "new orleans funk", "new orleans indie", "new orleans jazz", "new orleans rap", "new orleans soul", "new rave", "new romantic", "new school turkce rap", "new tejano", "new tribe", "new wave", "new wave of glam metal", "new wave of osdm", "new wave of screamo", "new wave of speed metal", "new wave of thrash metal", "new wave pop", "new weird america", "new weird finland", "new york death metal", "new york drill", "new york shoegaze", "new zealand classical", "newcastle indie", "newcastle nsw indie", "newfoundland indie", "ney", "ngoni", "nhac thieu nhi", "nice indie", "nigerian hip hop", "nigerian pop", "night drive phonk", "nightcore", "nightrun", "nijisanji", "ninja", "nintendocore", "nisiotika", "nitzhonot", "nl folk", "no beat", "no wave", "noel quebecois", "nohay", "noise", "noise pop", "noise punk", "noise rock", "noisecore", "nordic ambient", "nordic classical piano", "nordic contemporary classical", "nordic folk", "nordic folk metal", "nordic house", "nordic orchestra", "nordic post-rock", "nordic shoegaze", "nordic soundtrack", "nordnorsk musikk", "nordnorsk ponk", "nordnorsk rap", "normal indie", "norman ok indie", "norrbotten indie", "norrlandsk hip hop", "norsk lovsang", "norske viser", "norteno", "norteno-sax", "north alabama indie", "north carolina emo", "north carolina hip hop", "north carolina indie", "north carolina metal", "north carolina roots", "north dakota indie", "north east england indie", "north moroccan rap", "northamptonshire indie", "northeast indian hip hop", "northeast indian indie", "northern irish indie", "northern irish punk", "northern soul", "northumbrian folk", "northwest china indie", "norwegian alternative rock", "norwegian americana", "norwegian black metal", "norwegian blues", "norwegian choir", "norwegian classical", "norwegian contemporary jazz", "norwegian country", "norwegian death metal", "norwegian doom metal", "norwegian experimental", "norwegian folk", "norwegian folk rock", "norwegian gospel", "norwegian hardcore", "norwegian hip hop", "norwegian house", "norwegian indie", "norwegian jazz", "norwegian metal", "norwegian pop", "norwegian pop rap", "norwegian prog", "norwegian psychedelic", "norwegian punk", "norwegian punk rock", "norwegian rock", "norwegian singer-songwriter", "norwegian space disco", "norwegian techno", "norwegian trap", "nottingham hip hop", "nottingham indie", "nouvelle chanson francaise", "nova canco", "nova mpb", "nova musica amazonense", "nova musica carioca", "nova musica maranhense", "nova musica paulista", "nova musica pernambucana", "novelty", "novo rock gaucho", "novos talentos brasileiros", "nu age", "nu disco", "nu electro", "nu gabber", "nu gaze", "nu jazz", "nu metal", "nu skool breaks", "nu-cumbia", "nu-metalcore", "nubian traditional", "nueva cancion", "nueva ola chilena", "nueva ola peruana", "nueva trova chilena", "nuevo flamenco", "nuevo folklore argentino", "nuevo folklore mexicano", "nuevo tango", "nurnberg indie", "nursery", "nwobhm", "nwocr", "nwothm", "ny roots", "nyahbinghi", "nyc club", "nyc indie rock", "nyc metal", "nyc pop", "nyc rap", "nyckelharpa", "nyhc", "nz alternative rock", "nz children's music", "nz christian", "nz dnb", "nz electronic", "nz folk", "nz gangsta rap", "nz hardcore", "nz hip hop", "nz indie", "nz jazz", "nz metal", "nz pop", "nz post-punk", "nz punk", "nz reggae", "nz singer-songwriter", "oakland hip hop", "oakland indie", "oaxaca indie", "oberkrainer", "oc indie", "oc rap", "occult black metal", "ocean", "oceania soundtrack", "odia bhajan", "odia pop", "oeteldonk", "ogene", "ohangla", "ohio hardcore", "ohio hip hop", "ohio indie", "oi", "ok indie", "okc indie", "okinawan folk", "okinawan pop", "oklahoma country", "oktoberfest", "old school atlanta hip hop", "old school bassline", "old school dancehall", "old school ebm", "old school hard trance", "old school highlife", "old school hip hop", "old school nederhop", "old school rap francais", "old school thrash", "old school uk hip hop", "old west", "old-time", "old-time fiddle", "oldschool deutschrap", "olympia wa indie", "omaha indie", "one-person band", "ontario indie", "opera", "opera chorus", "opera metal", "operatic pop", "operetta", "opm", "oratory", "orchestra", "orchestral performance", "orchestral soundtrack", "orebro indie", "organetto", "organic ambient", "organic electronic", "organic house", "orgcore", "oriental classical", "oriental metal", "orkiestra symfoniczna", "orkney and shetland folk", "orlando indie", "oromo pop", "orquesta cubana", "orquesta tipica", "orquesta tropical", "orquestas de galicia", "orthodox chant", "oshare kei", "oslo indie", "ostrock", "ostschlager", "otacore", "oth indie", "otroske pesmice", "ottawa indie", "ottawa rap", "oud", "oulu indie", "oulu metal", "outer hip hop", "outlaw country", "outsider", "outsider house", "oxford choir", "oxford indie", "oyun havasi", "p funk", "p-pop", "pacific islands gospel", "pacific islands pop", "pagan black metal", "pagode", "pagode baiano", "pagode novo", "pahadi pop", "paidika tragoudia", "paisley underground", "pakistani electronic", "pakistani folk", "pakistani hip hop", "pakistani indie", "pakistani pop", "pakistani rock", "palestinian alternative", "palestinian hip hop", "palestinian pop", "palestinian traditional", "palm desert scene", "palm wine guitar", "panamanian indie", "panamanian pop", "panamanian rock", "panpipe", "pansori", "papuan traditional", "papuri", "paracana", "paraguayan indie", "paraguayan rock", "parody", "partido alto", "partyschlager", "pashto pop", "pasodobles", "pastoral", "pei indie", "pennsylvania hardcore", "pennsylvania shoegaze", "permanent wave", "perreo", "persian alternative", "persian drill", "persian electronic", "persian hip hop", "persian melodic rap", "persian neo-traditional", "persian poetry", "persian pop", "persian rock", "persian sad rap", "persian traditional", "persian trap", "persian underground hip hop", "perth hip hop", "perth indie", "peruvian death metal", "peruvian experimental", "peruvian hip hop", "peruvian indie", "peruvian metal", "peruvian punk", "peruvian rock", "pet calming", "philly drill", "philly indie", "philly rap", "philly soul", "phleng phuea chiwit", "phoenix indie", "phonk", "phonk brasileiro", "piada", "pianissimo", "piano blues", "piano cover", "piano house", "piano mpb", "piano rock", "piano worship", "pibroch", "picopop", "piedmont blues", "pilates", "pink noise", "pinoy alternative rap", "pinoy alternative rock", "pinoy city pop", "pinoy drill", "pinoy edm", "pinoy hip hop", "pinoy idol pop", "pinoy indie", "pinoy indie rock", "pinoy metal", "pinoy pop punk", "pinoy praise", "pinoy r&b", "pinoy reggae", "pinoy rock", "pinoy shoegaze", "pinoy singer-songwriter", "pinoy traditional", "pinoy trap", "pipa", "pirate", "piratenmuziek", "piseiro", "pittsburgh indie", "pittsburgh indie rock", "pittsburgh metal", "pittsburgh rap", "pittsburgh rock", "pixel", "pixie", "plena uruguaya", "plug brasileiro", "plugg", "plugg en espanol", "plugg francais", "pluggnb", "plunderphonics", "png pop", "poetry", "poezja spiewana", "pohadky", "pokemon", "polca paraguaya", "police band", "polish alternative", "polish alternative rap", "polish alternative rock", "polish ambient", "polish black metal", "polish blues", "polish choir", "polish classical", "polish classical piano", "polish contemporary classical", "polish death metal", "polish drill", "polish early music", "polish electronica", "polish emo", "polish experimental", "polish experimental electronic", "polish folk", "polish folk metal", "polish free jazz", "polish hardcore", "polish hip hop", "polish indie", "polish indie rock", "polish jazz", "polish metal", "polish metalcore", "polish modern jazz", "polish noise rock", "polish old school hip hop", "polish phonk", "polish pop", "polish post-punk", "polish post-rock", "polish prog", "polish psychedelia", "polish punk", "polish reggae", "polish rock", "polish shoegaze", "polish synthpop", "polish techno", "polish thrash metal", "polish trap", "polish underground rap", "polish viral pop", "polish viral rap", "political hip hop", "polka", "polka nortena", "polynesian hip hop", "polynesian traditional", "polyphonies corses", "polyphony", "pontian folk", "pontianak indie", "pony", "pop", "pop ambient", "pop argentino", "pop boliviano", "pop catracho", "pop chileno", "pop costarricense", "pop cristiano", "pop dance", "pop edm", "pop electronico", "pop emo", "pop flamenco", "pop folk", "pop house", "pop lgbtq+ brasileira", "pop minang", "pop nacional", "pop nacional antigas", "pop paraguayo", "pop peruano", "pop punk", "pop quebecois", "pop r&b", "pop rap", "pop rap brasileiro", "pop reggaeton", "pop rock", "pop rock brasileiro", "pop romantico", "pop soul", "pop teen brasileiro", "pop urbaine", "pop venezolano", "pop violin", "pop virale italiano", "pop worship", "popgaze", "popping", "pops orchestra", "popullore jugu", "popwave", "pornogrind", "porro", "portland hip hop", "portland indie", "portland metal", "portland punk", "portsmouth indie", "portuguese black metal", "portuguese classical", "portuguese contemporary classical", "portuguese death metal", "portuguese early music", "portuguese electronic", "portuguese experimental", "portuguese folk", "portuguese hardcore", "portuguese indie", "portuguese indie rock", "portuguese jazz", "portuguese metal", "portuguese pop", "portuguese post-rock", "portuguese rock", "portuguese techno", "post-black metal", "post-disco", "post-disco soul", "post-doom metal", "post-grunge", "post-hardcore", "post-hardcore chileno", "post-metal", "post-minimalism", "post-post-hardcore", "post-punk", "post-punk argentina", "post-punk brasileiro", "post-punk colombiano", "post-punk latinoamericano", "post-punk mexicano", "post-rock", "post-rock latinoamericano", "post-romantic era", "post-screamo", "post-teen pop", "pov: indie", "power blues-rock", "power electronics", "power metal", "power noise", "power pop", "power thrash", "power-pop punk", "powerviolence", "powwow", "poznan indie", "prague indie", "praise", "prank", "pre-war blues", "precure", "prepared piano", "preschool children's music", "pretty rhythm", "previa", "prog metal", "prog quebec", "progressive alternative", "progressive black metal", "progressive bluegrass", "progressive breaks", "progressive death metal", "progressive deathcore", "progressive doom", "progressive electro house", "progressive groove metal", "progressive house", "progressive jazz fusion", "progressive metal", "progressive metalcore", "progressive post-hardcore", "progressive power metal", "progressive psytrance", "progressive rock", "progressive sludge", "progressive technical death metal", "progressive thrash", "progressive trance", "progressive trance house", "progressive uplifting trance", "protest folk", "proto-hyperpop", "proto-metal", "proto-rap", "proto-techno", "protopunk", "psalmen", "psalms", "psicodelia brasileira", "psicodelia chilena", "psicodelia mexicana", "psybass", "psybreaks", "psych gaze", "psychedelic blues-rock", "psychedelic doom", "psychedelic folk", "psychedelic folk rock", "psychedelic hip hop", "psychedelic jazz fusion", "psychedelic pop", "psychedelic punk", "psychedelic rock", "psychedelic soul", "psychedelic space rock", "psychedelic trance", "psychill", "psychobilly", "psychokore", "psydub", "psytech", "pub rock", "puerto rican folk", "puerto rican indie", "puerto rican metal", "puerto rican pop", "puerto rican rock", "puglia indie", "puirt-a-beul", "pune indie", "punjabi folk", "punjabi hip hop", "punjabi lo-fi", "punjabi pop", "punk", "punk 'n' roll", "punk blues", "punk catala", "punk chileno", "punk colombiano", "punk cover", "punk ecuatoriano", "punk euskera", "punk galego", "punk melodico chileno", "punk mexicano", "punk rock italiano", "punk rock mexicano", "punk ska", "punk tico", "punk tuga", "punk urbano", "punta", "punta rock", "purple sound", "purulia pop", "pygmy music", "q-pop", "qanun", "qawwali", "quantum sound", "quarteto gospel", "quartetto d'archi", "quatuor a cordes", "quebec death metal", "quebec hardcore", "quebec indie", "quebec metal", "quebec punk", "queens hip hop", "queer country", "queercore", "quiet storm", "quran", "r&b", "r&b argentino", "r&b brasileiro", "r&b en espanol", "r&b francais", "r&b italiano", "r&drill", "rabindra sangeet", "rabm", "raboday", "radio symphony", "raga rock", "rage rap", "ragga jungle", "raggatek", "ragtime", "rai", "rai algerien", "rain", "rajasthani folk", "rajasthani pop", "rakugo", "rally house", "ramonescore", "ranchera", "rap", "rap abc paulista", "rap acreano", "rap alagoano", "rap algerien", "rap angolano", "rap anime", "rap antillais", "rap baiano", "rap baixada fluminense", "rap belge", "rap boricua", "rap burkinabe", "rap calme", "rap canario", "rap capixaba", "rap catala", "rap catarinense", "rap cearense", "rap chileno", "rap chretien", "rap conciencia", "rap congolais", "rap conscient", "rap criolo", "rap cristao", "rap cristiano", "rap df", "rap dominicano", "rap ecuatoguineano", "rap ecuatoriano", "rap espanol", "rap euskera", "rap femenino mexicano", "rap feminino chileno", "rap feminino nacional", "rap francais", "rap francais nouvelle vague", "rap gabonais", "rap galego", "rap gasy", "rap gaucho", "rap geek", "rap genovese", "rap guarulhense", "rap guineen", "rap inde", "rap italiano old school", "rap ivoire", "rap kreyol", "rap latina", "rap liegeois", "rap lyonnais", "rap malien", "rap maroc", "rap maromba", "rap marseille", "rap metal", "rap metal espanol", "rap metalcore", "rap mineiro", "rap mocambicana", "rap moldovenesc", "rap montrealais", "rap motywacja", "rap nacional antigo", "rap napoletano", "rap nica", "rap norteno chileno", "rap nortista", "rap paraense", "rap paraguayo", "rap paranaense", "rap pernambucano", "rap politico", "rap portuense", "rap potiguar", "rap regio", "rap rock", "rap romantico", "rap salvadoreno", "rap sardegna", "rap sergipano", "rap siciliano", "rap sureno chileno", "rap tico", "rap toscana", "rap tuga underground", "rap tunisien", "rap uliczny", "rap underground argentino", "rap underground colombiano", "rap underground espanol", "rap underground mexicano", "rap uruguayo", "rare groove", "rasin", "rasiya", "raspe", "rautalanka", "rave", "rave funk", "raw black metal", "raw techno", "rawstyle", "re:techno", "reading", "reading indie", "rebel blues", "rebetiko", "recorder", "red dirt", "redneck", "reggae", "reggae boliviano", "reggae catala", "reggae cover", "reggae cristao", "reggae do maranhao", "reggae en espanol", "reggae fusion", "reggae gaucho", "reggae maghreb", "reggae mexicano", "reggae peruano", "reggae rock", "reggae tico", "reggae tuga", "reggae uruguayo", "reggaeton", "reggaeton chileno", "reggaeton colombiano", "reggaeton cristiano", "reggaeton flow", "reggaeton mexicano", "regional mexicano femenil", "reiki", "relaxative", "remix brasileiro", "remix product", "renaissance", "rennes indie", "reparto", "retro metal", "retro soul", "reunion pop", "rez country", "rhode island indie", "rhode island rap", "rhythm and blues", "rhythm and boogie", "rhythm game", "rhythm rock", "riddim", "riddim dubstep", "rif", "ringtone", "rio grande do sul indie", "riot grrrl", "ritmo kombina", "ritual ambient", "rkt", "rochester mn indie", "rochester ny indie", "rock", "rock abc paulista", "rock alagoano", "rock alternatif francais", "rock alternativo brasileiro", "rock alternativo espanol", "rock andaluz", "rock baiano", "rock brasiliense", "rock caipira", "rock campineiro", "rock catala", "rock catarinense", "rock catracho", "rock cearense", "rock chapin", "rock cristao fluminense", "rock cristiano", "rock curitibano", "rock dominicano", "rock drums", "rock en asturiano", "rock en espanol", "rock gaucho", "rock goiano", "rock gospel brasileiro", "rock gotico", "rock in opposition", "rock independant francais", "rock kapak", "rock keyboard", "rock mineiro", "rock nacional", "rock nacional brasileiro", "rock nacional feminino", "rock nica", "rock noise", "rock of gibraltar", "rock paraense", "rock paraibano", "rock pernambucano", "rock piauiense", "rock potiguar", "rock progresivo mexicano", "rock progressif francais", "rock quebecois", "rock sergipano", "rock sul-mato-grossense", "rock tico", "rock urbano mexicano", "rock uruguayo", "rock viet", "rock-and-roll", "rockabilly", "rockabilly en espanol", "rocksteady", "roda de samba", "rogaland indie", "rogaland musikk", "romanian black metal", "romanian classical piano", "romanian contemporary classical", "romanian electronic", "romanian folk", "romanian house", "romanian indie", "romanian metal", "romanian pop", "romanian punk", "romanian rap", "romanian rock", "romanian trap", "romantico", "rome indie", "rominimal", "rondalla", "rongmei pop", "roots americana", "roots reggae", "roots rock", "roots worship", "rosario indie", "rosary", "rotterdam indie", "rozpravky", "rumba", "rumba catalana", "rumba congolaise", "rumeli turkuleri", "rune folk", "russelater", "russian alt pop", "russian alternative rock", "russian black metal", "russian ccm", "russian chanson", "russian choir", "russian classical piano", "russian contemporary classical", "russian dance", "russian dance pop", "russian death metal", "russian dnb", "russian drain", "russian drill", "russian edm", "russian electronic", "russian emo", "russian emo rap", "russian experimental electronic", "russian folk", "russian folk metal", "russian folk rock", "russian gangster rap", "russian grime", "russian hardcore", "russian heavy metal", "russian hip hop", "russian hyperpop", "russian indie", "russian indie rock", "russian jazz", "russian metal", "russian metalcore", "russian modern classical", "russian modern jazz", "russian nu metal", "russian oi", "russian old school hip hop", "russian orchestra", "russian pixel", "russian plugg", "russian pop", "russian pop punk", "russian post-punk", "russian post-rock", "russian power metal", "russian punk", "russian punk rock", "russian rave", "russian reggae", "russian rock", "russian romance", "russian romanticism", "russian screamo", "russian shoegaze", "russian ska", "russian synthpop", "russian techno", "russian thrash metal", "russian trance", "russian trap", "russian trap metal", "russian underground rap", "russian viral pop", "russian viral rap", "russian witch house", "rusyn folk", "ruta destroy", "rva drill", "rva indie", "rwandan gospel", "rwandan hip hop", "rwandan pop", "rwandan traditional", "ryukoka", "ryukyu ongaku", "sacramento hip hop", "sacramento indie", "sacred harp", "sacred steel", "sad lo-fi", "sad rap", "sad sierreno", "sadcore", "sakura wars", "salay", "salon music", "salsa", "salsa choke", "salsa colombiana", "salsa cristiana", "salsa cubana", "salsa international", "salsa peruana", "salsa puertorriquena", "salsa urbana", "salsa venezolana", "salzburg indie", "samba", "samba de roda", "samba gospel", "samba moderno", "samba paulista", "samba reggae", "samba-enredo", "samba-jazz", "samba-rock", "sambalpuri pop", "sambass", "sami", "samoan pop", "samurai trap", "san antonio indie", "san antonio rap", "san diego indie", "san diego rap", "san marcos tx indie", "sandalwood", "sanfona", "santa fe indie", "santali pop", "santoor", "santur", "saraiki pop", "sarangi", "sardinia indie", "sarod", "saskatchewan indie", "sasscore", "saxony metal", "saxophone house", "saxophone trio", "scam rap", "scandinavian r&b", "scandipop", "scenecore", "schlager", "school choir", "school ensemble", "schrammelmusik", "schranz", "schweizer rap", "schwyzerorgeli", "sci-fi metal", "scorecore", "scottish americana", "scottish drill", "scottish electronic", "scottish fiddle", "scottish folk", "scottish gaelic folk", "scottish hip hop", "scottish hush", "scottish indie", "scottish indie folk", "scottish indie rock", "scottish jazz", "scottish metal", "scottish new wave", "scottish rock", "scottish shoegaze", "scottish singer-songwriter", "scottish smallpipe", "scottish techno", "scouse rap", "scratch", "scream rap", "screamo", "screamocore", "sda a cappella", "sda choir", "sean-nos singing", "seattle hip hop", "seattle indie", "seattle metal", "sebene", "second line", "seemannslieder", "sefardi", "sega", "sega mauricien", "seggae", "seinen", "seiyu", "semarang indie", "semba", "senegalese traditional", "sepedi pop", "serbian alternative rock", "serbian electronic", "serbian folk", "serbian hip hop", "serbian indie", "serbian metal", "serialism", "sertanejo", "sertanejo gospel", "sertanejo pop", "sertanejo tradicional", "sertanejo universitario", "sesame street", "sesotho hip hop", "sesotho pop", "sevdah", "sevilla indie", "sevillanas", "seychelles pop", "sgija", "shaabi", "shabad", "shakuhachi", "shamanic", "shamisen", "shanghai indie", "shanty", "shantykoren", "shatta", "sheffield indie", "shehnai", "sheilat", "shib", "shibuya-kei", "shimmer pop", "shimmer psych", "shiver pop", "shoegaze", "shoegaze argentino", "shoegaze brasileiro", "shoegaze chileno", "shoegaze mexicano", "shoegaze peruano", "shojo", "sholawat", "shonen", "show tunes", "shred", "shush", "siberian folk", "sichuanese hip hop", "sierra leonean pop", "sierreno", "sigilkore", "sikkim indie", "sillycore", "sinaloa indie", "sindhi", "singaporean electronic", "singaporean hip hop", "singaporean indie", "singaporean mandopop", "singaporean metal", "singaporean pop", "singaporean punk", "singaporean singer-songwriter", "singeli", "singer-songwriter", "singer-songwriter pop", "singing bowl", "sinhala edm", "sinhala indie", "sinhala pop", "sinhala rap", "sinogaze", "sirmauri pop", "sitar", "ska", "ska argentino", "ska catala", "ska chileno", "ska espanol", "ska jazz", "ska mexicano", "ska punk", "ska revival", "skansk musik", "skate punk", "skiffle", "skinhead oi", "skramz", "skweee", "sky room", "slack-key guitar", "slacker rock", "slam death metal", "slam poetry", "slamming deathcore", "slap house", "slash punk", "slaskie piosenki", "slavic folk metal", "slayer", "slc hardcore", "slc indie", "sleaze rock", "sleep", "slovak electronic", "slovak folk", "slovak hip hop", "slovak indie", "slovak metal", "slovak pop", "slovak punk", "slovak rock", "slovak trap", "slovenian electronic", "slovenian folk", "slovenian hip hop", "slovenian indie", "slovenian metal", "slovenian pop", "slovenian rock", "slovenske chvaly", "slow game", "slowcore", "slowed and reverb", "sludge metal", "sludgecore", "slushwave", "small room", "smooth jazz", "smooth saxophone", "smooth soul", "smutny rap", "soca", "socal indie", "socal pop punk", "social media pop", "soda pop", "soft rock", "solfeggio product", "solipsynthm", "solo wave", "solomon islands pop", "somali pop", "somatik techno", "son cubano", "son cubano clasico", "son jarocho", "song poem", "sonora indie", "sophisti-pop", "sorani pop", "sotalaulut", "soukous", "soul", "soul blues", "soul flow", "soul jazz", "souldies", "soulful house", "sound", "sound art", "sound collage", "sound effects", "sound team", "soundtrack", "south african alternative", "south african choral", "south african country", "south african deep house", "south african dnb", "south african electronic", "south african gospel", "south african hip hop", "south african house", "south african jazz", "south african metal", "south african modern jazz", "south african pop", "south african pop dance", "south african punk", "south african r&b", "south african rock", "south african soulful deep house", "south african techno", "south african trap", "south african underground rap", "south asian metal", "south borneo indie", "south carolina hip hop", "south carolina indie", "south carolina metal", "south dakota indie", "south sudanese pop", "southampton indie", "southeast asian post-rock", "southern americana", "southern china indie", "southern gospel", "southern hip hop", "southern metal", "southern rock", "southern soul", "southern soul blues", "southwestern china indie", "soviet synthpop", "sovietwave", "spa", "space age pop", "space ambient", "space rock", "spacegrunge", "spacesynth", "spacewave", "spanish baroque", "spanish black metal", "spanish blues", "spanish classical", "spanish classical piano", "spanish contemporary classical", "spanish death metal", "spanish electronic", "spanish electropop", "spanish experimental", "spanish folk", "spanish folk metal", "spanish folk rock", "spanish hip hop", "spanish indie folk", "spanish indie pop", "spanish indie rock", "spanish invasion", "spanish jazz", "spanish metal", "spanish modern rock", "spanish new wave", "spanish noise pop", "spanish pop", "spanish pop rock", "spanish post-punk", "spanish post-rock", "spanish prog", "spanish progressive rock", "spanish psychedelic rock", "spanish punk", "spanish reggae", "spanish renaissance", "spanish rock", "spanish rockabilly", "spanish shoegaze", "spanish stoner rock", "spanish synthpop", "spanish techno", "spectra", "sped up", "speed garage", "speed house", "speed metal", "speed plug brasileiro", "speed up brasileiro", "speed up turkce", "speedcore", "speedrun", "spiritual hip hop", "spiritual jazz", "spirituals", "spoken word", "springfield mo indie", "spytrack", "st louis drill", "st louis rap", "st petersburg fl indie", "staff band", "starmyu", "starogradska", "stateside dnb", "steampunk", "steel guitar", "steelpan", "stenchcore", "stl indie", "stockholm indie", "stomp and flutter", "stomp and holler", "stomp and whittle", "stomp pop", "stoner metal", "stoner rock", "straight edge", "straight-ahead jazz", "streektaal", "street band", "street punk", "street punk espanol", "streichquartett", "stride", "string band", "string duo", "string folk", "string orchestra", "string quartet", "string quintet", "strut", "stubenmusik", "study beats", "stutter house", "stuttgart indie", "subliminal product", "substep", "sudanese hip hop", "sudanese pop", "sufi", "sufi chant", "sulawesi indie", "sundanese traditional", "sung poetry", "sungura", "sunnlensk tonlist", "sunset lounge", "sunshine pop", "suomi rock", "suomirap", "suomisaundi", "super eurobeat", "super sentai", "supergroup", "surabaya indie", "surf music", "surf punk", "surinamese hip hop", "surinamese pop", "svensk indie", "svensk lovsang", "svensk progg", "swahili gospel", "swamp blues", "swamp pop", "swamp rock", "swancore", "swansea indie", "swazi hip hop", "swazi pop", "swazi traditional", "swedish alternative rock", "swedish americana", "swedish black metal", "swedish blues", "swedish choir", "swedish classical", "swedish contemporary classical", "swedish country", "swedish dancehall", "swedish death metal", "swedish doom metal", "swedish drill", "swedish ebm", "swedish electronic", "swedish electropop", "swedish emo", "swedish eurodance", "swedish experimental", "swedish fiddle", "swedish folk pop", "swedish gangsta rap", "swedish garage rock", "swedish grindcore", "swedish hard rock", "swedish hardcore", "swedish heavy metal", "swedish hip hop", "swedish house", "swedish idol pop", "swedish indie folk", "swedish indie pop", "swedish indie rock", "swedish jazz", "swedish jazz orkester", "swedish melodeath", "swedish melodic rock", "swedish metal", "swedish metalcore", "swedish pop", "swedish pop punk", "swedish pop rap", "swedish post-hardcore", "swedish post-punk", "swedish power metal", "swedish prog", "swedish progressive metal", "swedish psychedelic rock", "swedish punk", "swedish reggae", "swedish rock-and-roll", "swedish rockabilly", "swedish singer-songwriter", "swedish soul", "swedish stoner rock", "swedish synth", "swedish synthpop", "swedish techno", "swedish trap", "swedish trap pop", "swedish tropical house", "swedish underground rap", "swing", "swing italiano", "swing revival", "swiss alternative rock", "swiss black metal", "swiss classical piano", "swiss contemporary classical", "swiss country", "swiss experimental", "swiss folk", "swiss hip hop", "swiss house", "swiss indie", "swiss indie folk", "swiss jazz", "swiss metal", "swiss pop", "swiss punk", "swiss reggae", "swiss rock", "swiss singer-songwriter", "swiss techno", "swiss trap", "swiss worship", "sydney indie", "symfonicky orchestr", "symphonic black metal", "symphonic death metal", "symphonic deathcore", "symphonic melodic death metal", "symphonic metal", "symphonic power metal", "symphonic rock", "synth funk", "synth prog", "synth punk", "synthesizer", "synthetic classical", "synthpop", "synthwave", "synthwave brasileiro", "syrian hip hop", "syrian pop", "syro-aramaic chant", "szanty", "t-pop", "t-pop boy group", "t-pop girl group", "taarab", "tabla", "tagalog rap", "tagalog worship", "tahitian traditional", "taiko", "taiwan campus folk", "taiwan classical performance", "taiwan electronic", "taiwan experimental", "taiwan graduation song", "taiwan hip hop", "taiwan idol pop", "taiwan indie", "taiwan instrumental", "taiwan metal", "taiwan pop", "taiwan post-rock", "taiwan punk", "taiwan rock", "taiwan singer-songwriter", "taiwanese indie", "taiwanese indigenous music", "taiwanese pop", "tajik pop", "tajik traditional", "talent show", "talentkonkurranse", "talentkonkurrence", "talentos brasileiros", "talentschau", "tallava", "tamaulipas indie", "tamaulipas rap", "tamazight", "tamborazo", "tamburica", "tamil devotional", "tamil hip hop", "tamil indie", "tamil indie hip hop", "tamil pop", "tamil worship", "tampa indie", "tan co", "tanci", "tango", "tango cancion", "tanzanian hip hop", "tanzanian pop", "tanzanian traditional", "tanzlmusi", "tanzorchester", "tape club", "tape music", "tar", "taraneem", "tarantella", "tassie indie", "tatar folk", "tatar pop", "tavern", "tearout", "tech house", "tech trance", "techengue", "technical black metal", "technical brutal death metal", "technical death metal", "technical deathcore", "technical grindcore", "technical groove metal", "technical melodic death metal", "technical thrash", "techno", "techno argentina", "techno kayo", "techno rave", "techno remix", "tecnobanda", "tecnobrega", "teen pop", "tejano", "tekk", "tekno", "telugu devotional", "telugu folk", "telugu hip hop", "telugu indie", "telugu remix", "telugu worship", "tempe indie", "tennessee experimental", "tennessee hip hop", "tennessee metal", "terrorcore", "tex-mex", "texas blues", "texas country", "texas death metal", "texas hardcore", "texas latin rap", "texas metal", "texas pop punk", "texas punk", "texasgaze", "thai bl ost", "thai folk", "thai folk pop", "thai folk rock", "thai hip hop", "thai indie", "thai indie pop", "thai indie rock", "thai instrumental", "thai metal", "thai ost", "thai pop", "thai pop rap", "thai post-rock", "thai psychedelic", "thai punk", "thai rock", "thai shoegaze", "thai teen pop", "thai traditional", "thai trap", "thai viral pop", "thai vtuber", "thai worship", "thall", "theme", "therapy", "theremin", "thrash core", "thrash metal", "thrash-groove metal", "throat singing", "tibetan folk pop", "tibetan hip hop", "tibetan mantra", "tibetan pop", "tibetan traditional", "tierra caliente", "tigrigna pop", "tijuana electronic", "tijuana indie", "timba", "tin pan alley", "tinku", "tipico", "togolese pop", "tolkien metal", "tollywood", "tololoche", "tone", "tongan pop", "tontipop", "torch song", "toronto indie", "toronto rap", "totalism", "touhou", "touken ranbu", "trad jazz catala", "trad quebecois", "traditional bluegrass", "traditional blues", "traditional british folk", "traditional country", "traditional english folk", "traditional folk", "traditional funk", "traditional irish singing", "traditional reggae", "traditional rockabilly", "traditional scottish folk", "traditional ska", "traditional soul", "traditional southern folk", "trallalero", "trallpunk", "trance", "trance brasileiro", "trance mexicano", "trancecore", "transpop", "trap", "trap angolano", "trap antillais", "trap argentino", "trap baiano", "trap beats", "trap boliviano", "trap boricua", "trap brasileiro", "trap carioca", "trap catala", "trap chileno", "trap colombiano", "trap cristao", "trap cristiano", "trap dominicano", "trap ecuatoriano", "trap funk", "trap italiana", "trap kreyol", "trap latino", "trap maroc", "trap metal italiana", "trap mexicano", "trap peruano", "trap pesado", "trap queen", "trap soul", "trap triste", "trap tuga", "trap venezolano", "traphall", "traprun", "trash rock", "trecento", "trekkspill", "triangle indie", "tribal ambient", "tribal house", "tribute", "trikiti", "trinibad", "trinidadian reggae", "trio batak", "trio cubano", "trio huasteco", "trip hop", "trival", "trombone brasileiro", "trombone ensemble", "trondersk musikk", "trondheim indie", "trop rock", "tropical", "tropical alternativo", "tropical house", "tropical tecladista", "tropicalia", "trot", "troubadour", "trouvere", "trova", "trova mexicana", "truck-driving country", "tsukiuta", "tuareg guitar", "tucson indie", "tulsa indie", "tulum", "tuna", "tuna universitaria", "tunantada", "tunisian alternative", "tunisian pop", "turbo folk", "turin indie", "turk sanat muzigi", "turkce drill", "turkce kadin rap", "turkce remix", "turkce slow sarkilar", "turkce trap metal", "turkish alt pop", "turkish alternative", "turkish alternative rock", "turkish black metal", "turkish classical", "turkish classical performance", "turkish death metal", "turkish deep house", "turkish edm", "turkish electronic", "turkish experimental", "turkish folk", "turkish hardcore", "turkish hip hop", "turkish instrumental", "turkish jazz", "turkish metal", "turkish modern jazz", "turkish pop", "turkish post-punk", "turkish psych", "turkish punk", "turkish reggae", "turkish rock", "turkish singer-songwriter", "turkish soundtrack", "turkish trap", "turkish trap pop", "turkmen hip hop", "turkmen pop", "turntablism", "tuvan folk", "twee indie pop", "twee pop", "twin cities indie", "twoubadou", "tzadik", "ua trap", "uae indie", "ugandan gospel", "ugandan hip hop", "ugandan pop", "ugandan traditional", "uilleann pipes", "uk alternative hip hop", "uk alternative pop", "uk americana", "uk bass", "uk beatdown", "uk christian rap", "uk contemporary jazz", "uk contemporary r&b", "uk dance", "uk dancehall", "uk desi rap", "uk diy punk", "uk dnb", "uk doom metal", "uk drill", "uk dub", "uk experimental electronic", "uk funky", "uk garage", "uk hip hop", "uk house", "uk melodic rap", "uk metalcore", "uk noise rock", "uk pop", "uk pop punk", "uk post-hardcore", "uk post-metal", "uk post-punk", "uk post-punk revival", "uk reggae", "uk rockabilly", "uk stoner rock", "uk tech house", "uk worship", "uk82", "ukg revival", "ukhc", "ukrainian alternative rock", "ukrainian ambient", "ukrainian black metal", "ukrainian ccm", "ukrainian choir", "ukrainian classical", "ukrainian classical piano", "ukrainian contemporary classical", "ukrainian dnb", "ukrainian edm", "ukrainian electronic", "ukrainian emo", "ukrainian experimental", "ukrainian folk", "ukrainian folk pop", "ukrainian folk rock", "ukrainian hip hop", "ukrainian indie", "ukrainian jazz", "ukrainian metal", "ukrainian metalcore", "ukrainian phonk", "ukrainian pop", "ukrainian post-punk", "ukrainian psychedelic", "ukrainian punk", "ukrainian rock", "ukrainian shoegaze", "ukrainian techno", "ukrainian viral pop", "ukulele", "ukulele cover", "ulkucu sarkilar", "uma musume", "umbanda", "umea hardcore", "umea indie", "unblack metal", "underground amapiano", "underground boom bap", "underground grunge", "underground hip hop", "underground power pop", "underground rap", "underground visual kei", "undertale", "university choir", "uplifting trance", "uppsala indie", "upstate ny rap", "uptempo hardcore", "urban contemporary", "urban kiz", "urbano chileno", "urbano ecuatoriano", "urbano espanol", "urbano latino", "urbano mexicano", "urdu hip hop", "uruguayan indie", "us power metal", "usbm", "utah indie", "utah metal", "utapri", "utopian virtual", "uwielbienie", "uyghur folk", "uyghur pop", "uzbek hip hop", "uzbek pop", "uzbek traditional", "v-pop", "vaikiskos dainos", "vallenato", "vallenato moderno", "vampiric black metal", "vancouver indie", "vancouver metal", "vancouver punk", "vanuatu music", "vapor house", "vapor pop", "vapor soul", "vapor twitch", "vaportrap", "vaporwave", "vaqueiro", "variete francaise", "varmland rock", "vaudeville", "vbs", "veena", "vegan straight edge", "vegas indie", "velha guarda", "venda pop", "venda rap", "venezuelan hip hop", "venezuelan indie", "venezuelan metal", "venezuelan rock", "veracruz indie", "vermont indie", "vgm instrumental", "vgm remix", "via", "victoria bc indie", "victorian britain", "video game music", "vienna indie", "viet chill rap", "viet edm", "viet instrumental", "viet lo-fi", "viet remix", "vietnamese bolero", "vietnamese electronic", "vietnamese hip hop", "vietnamese idol pop", "vietnamese melodic rap", "vietnamese pop", "vietnamese singer-songwriter", "vietnamese traditional", "vietnamese trap", "viking black metal", "viking folk", "viking metal", "villancicos", "vinahouse", "vincy soca", "vintage broadway", "vintage cantonese pop", "vintage chanson", "vintage chinese pop", "vintage classical singing", "vintage country folk", "vintage dutch pop", "vintage finnish jazz", "vintage french electronic", "vintage french psychedelic", "vintage gospel", "vintage hawaiian", "vintage hollywood", "vintage italian pop", "vintage italian soundtrack", "vintage jazz", "vintage norwegian pop", "vintage old-time", "vintage radio show", "vintage reggae", "vintage rockabilly", "vintage schlager", "vintage spanish pop", "vintage swedish pop", "vintage swing", "vintage swoon", "vintage taiwan pop", "vintage tango", "vintage tollywood", "vintage western", "viola", "viola caipira", "viola da gamba", "violao", "violao classico", "violin", "viral afropop", "viral pop", "viral pop brasileiro", "viral rap", "viral trap", "virgin islands reggae", "virginia hip hop", "virginia indie", "virginia metal", "virginia punk", "visor", "vispop", "visual kei", "vlaamse cabaret", "vlaamse kinderliedje", "vlaamse rap", "vocal ensemble", "vocal harmony group", "vocal house", "vocal jazz", "vocal resources", "vocal trance", "vocaloid", "vocaloid metal", "vocaloid rock", "voetbal", "vogue", "voidgaze", "voidgrind", "volksmusik", "volkspop", "volkstumliche musik", "wagnerian singing", "waiata maori", "waiata mo tamariki", "wandelweiser", "war metal", "warm drone", "warrington indie", "washboard", "washington indie", "wassoulou", "water", "wave", "weightless", "weirdcore", "wellington indie", "welsh choir", "welsh folk", "welsh hip hop", "welsh indie", "welsh metal", "welsh rock", "west african jazz", "west australian hip hop", "west bengali pop", "west coast rap", "west coast reggae", "west coast trap", "west end", "west virginia indie", "west virginia metal", "west yorkshire indie", "west-vlaamse hip hop", "westcoast flow", "western americana", "western mass indie", "western ny metal", "western saharan folk", "western swing", "whale song", "white noise", "wind ensemble", "wind quintet", "wind symphony", "windsor on indie", "winnipeg hip hop", "wisconsin indie", "wisconsin metal", "witch house", "women's choir", "women's music", "wonky", "worcester ma indie", "workout product", "world", "world chill", "world devotional", "world fusion", "world meditation", "world worship", "worship", "wrestling", "writing", "wrock", "wu fam", "wuhan indie", "wyoming indie", "wyoming roots", "xenharmonic", "xhosa", "xhosa hip hop", "xinyao", "xitsonga pop", "xtra raw", "yacht rock", "yakut pop", "yakuza", "yaoi", "ye ye", "yemeni pop", "yemeni traditional", "yiddish folk", "yodeling", "yoga", "yogyakarta indie", "yoik", "york indie", "yorkshire folk", "yoruba worship", "youth orchestra", "yowapeda", "yu-mex", "yugoslav new wave", "yugoslav rock", "yunnan traditional", "yuri", "zamba", "zambian gospel", "zambian hip hop", "zambian pop", "zampogna", "zarzuela", "zcc", "zen", "zenonesque", "zespol dzieciecy", "zeuhl", "zhenskiy rep", "zhongguo feng", "zikir", "zilizopendwa", "zillertal", "zim gospel", "zim hip hop", "zim urban groove", "zimdancehall", "zither", "zohioliin duu", "zolo", "zomi pop", "zoomergaze", "zouglou", "zouk", "zouk riddim", "zurich indie", "zxc", "zydeco" };
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
