quadule/knobby/src/ImprovSerial.h

#pragma once

#include <improv.h>
#include <HardwareSerial.h>
#include <WiFi.h>

enum ImprovSerialType : uint8_t {
  TYPE_CURRENT_STATE = 0x01,
  TYPE_ERROR_STATE = 0x02,
  TYPE_RPC = 0x03,
  TYPE_RPC_RESPONSE = 0x04
};

static const uint8_t IMPROV_SERIAL_VERSION = 1;

class ImprovSerial {
 public:
  void setup(std::string name);
  bool loop();
  improv::State getState();
  std::string getSSID();
  std::string getPassword();

 protected:
  bool parseByte(uint8_t byte);
  bool parsePayload(improv::ImprovCommand &command);

  void setState(improv::State state);
  void setError(improv::Error error);
  void sendResponse(std::vector<uint8_t> &response);
  void onWiFiConnectTimeout();

  std::vector<uint8_t> buildResponse(improv::Command command);
  std::vector<uint8_t> buildVersionInfo();

  uint8_t readByte();
  void writeData(std::vector<uint8_t> &data);

  std::vector<uint8_t> _rxBuffer;
  uint32_t _lastReadByte{0};
  improv::State _state{improv::STATE_AUTHORIZED};
  improv::ImprovCommand _command{improv::Command::UNKNOWN, "", ""};

  std::string _firmwareName = std::string("knobby");
  std::string _firmwareVersion = std::string(KNOBBY_VERSION);
  std::string _hardwareVariant = std::string(PLATFORMIO_ENV);
  std::string _deviceName;
};

extern ImprovSerial improvSerial;
